Phil-CIA/Solar-Project-200w/hardware/mppt/net-plan.md

# MPPT Net Plan (Draft)

Last updated: 2026-07-14
Purpose: keep schematic net naming consistent and traceable from day one.

## 1. Naming Conventions

- Power nets: ALL_CAPS with domain and polarity suffix.
- Sense nets: SENSE_<DOMAIN>_<MEASURED>
- Control nets: CTRL_<FUNCTION>
- Fault nets: FAULT_<TYPE>
- Logging nets: UART_<DIR>_<ROLE>
- KiCad implementation style: use global labels for canonical inter-zone nets in the single-sheet schematic.
- Layout style: rectangles are used as functional zones (Sheet 1/2/3/4 intent), not separate hierarchical sheets.

## 2. Candidate Net List

| Net Name | Domain | Direction | Purpose | Requirement Link |
|---|---|---|---|---|
| PV_IN_POS_RAW | PV Input | In | Raw positive input before fuse and reverse protection | REQ-SAF-004 |
| PV_IN_POS_FUSED | PV Input | Internal | Positive input after fuse and before reverse protection element | REQ-SAF-004 |
| PV_IN_POS | PV Input | In | Positive PV input rail | REQ-PV-001 |
| PWR_NEG | Shared Return | Bidirectional | Canonical shared negative return rail across PV, charger output, and battery interface | REQ-PV-001, REQ-CHG-001, REQ-BAT-001 |
| MPPT_SW_NODE | Power Stage | Internal | Main switching node for conversion stage | REQ-CHG-001 |
| CHG_OUT_POS | Charger Output | Out | Charger positive output to battery interface | REQ-CHG-001 |
| BAT_BUS_POS | Battery Bus | Bidirectional | Battery positive bus boundary | REQ-BAT-001 |
| CTRL_SUPPLY_IN | Control Power | In | Protected control-domain input boundary after source OR-ing (PV and optional battery assist path) | REQ-SAF-003, REQ-TEL-002 |
| USB_5V_IN | Control Power | In | USB bench-power boundary used when PV is absent | REQ-TEL-001 |
| CTRL_3V3 | Control Power | Out | Main 3.3V control rail for STM32G431 digital supply and control I/O pull domains | REQ-TEL-002 |
| CTRL_3V3A | Control Power | Out | Filtered analog 3.3V rail for ADC/reference-sensitive nodes (can be linked to CTRL_3V3 in first pass) | REQ-TEL-002 |
| SENSE_PV_V | Sensing | In | PV voltage feedback channel | REQ-TEL-002 |
| SENSE_PV_I | Sensing | In | PV current feedback channel | REQ-TEL-002 |
| SENSE_BAT_V | Sensing | In | Battery voltage feedback channel | REQ-TEL-002 |
| SENSE_BAT_I | Sensing | In | Battery current feedback channel | REQ-TEL-002 |
| SENSE_TEMP_PWR | Sensing | In | Power stage thermal monitor | REQ-TEL-002 |
| SENSE_TEMP_BOARD | Sensing | In | Board ambient/control thermal monitor | REQ-TEL-002 |
| CTRL_PWM_MAIN | Control | Out | Main PWM drive/control command | REQ-CHG-001 |
| GATE_Q1 | Control | Out | Gate drive net to buck high-side MOSFET | REQ-CHG-001 |
| CTRL_EN_CHG | Control | Out | Charger enable/disable control | REQ-SAF-003 |
| BTN_UP_N | Control (UI) | In | Navigation button input (up), active-low | REQ-TEL-003 |
| BTN_DN_N | Control (UI) | In | Navigation button input (down), active-low | REQ-TEL-003 |
| BTN_LT_N | Control (UI) | In | Navigation button input (left), active-low | REQ-TEL-003 |
| BTN_RT_N | Control (UI) | In | Navigation button input (right), active-low | REQ-TEL-003 |
| BTN_ENT_N | Control (UI) | In | Navigation button input (enter/center), active-low | REQ-TEL-003 |
| FAULT_OCP | Protection | Out | Over-current fault signal | REQ-SAF-003 |
| FAULT_OVP | Protection | Out | Over-voltage fault signal | REQ-SAF-003 |
| UART_TX_LOG | Telemetry | Out | Serial logging transmitter | REQ-TEL-001 |
| UART_RX_CFG | Telemetry | In | Serial configuration/command receiver | REQ-TEL-001 |
| MCU_RST_N | Control | In | STM32 external reset net from button/debug path, active-low | REQ-SAF-006 |
| MCU_HSE_IN | Clock | In | STM32 external high-speed crystal input | REQ-VAL-003 |
| MCU_HSE_OUT | Clock | Out | STM32 external high-speed crystal output | REQ-VAL-003 |

## 3. Notes

- Final net names may evolve, but ID continuity should be preserved where possible.
- If a net name changes, update this file and record the reason in decisions-log.
- Current canonical negative return net is `PWR_NEG`; legacy per-zone negative names are retired for this single-sheet implementation.
- DEC-013 defines source-priority behavior for Rev 0 control power: PV-first runtime path, optional battery assist to `CTRL_SUPPLY_IN`, and protected USB fallback for bench operation when PV is absent.
- Q-004 is closed: the U4 wide-input control-supply path is the Rev 0 `CTRL_3V3` owner architecture; U2 path is not the intended live owner in final Rev 0 implementation.
