Phil-CIA/Solar-Project-200w/hardware/kicad/solar-project/report.txt

Info: Processing symbol 'C1:PCM_JLCPCB:C_0805'.
Info: Processing symbol 'C28:PCM_JLCPCB:C_0805'.
Info: Processing symbol 'C11:PCM_JLCPCB:C_1206'.
Info: Processing symbol 'R5:PCM_JLCPCB:R_0805'.
Info: Processing symbol 'C36:Capacitor_THT:CP_Radial_D6.3mm_P2.50mm'.
Info: Processing symbol 'R4:PCM_JLCPCB:R_0805'.
Info: Processing symbol 'R3:PCM_JLCPCB:R_0805'.
Info: Processing symbol 'R12:PCM_JLCPCB:R_0805'.
Info: Processing symbol 'L3:Inductor_SMD:L_KOHERelec_MDA7030'.
Info: Processing symbol 'C50:PCM_JLCPCB:C_0805'.
Info: Processing symbol 'D5:PCM_JLCPCB:D_DO-214AC(SMA)'.
Info: Processing symbol 'F1:Fuse:Fuseholder_Littelfuse_100_series_5x25mm'.
Info: Processing symbol 'C21:Capacitor_SMD:CP_Elec_10x12.6'.
Info: Processing symbol 'C2:PCM_JLCPCB:C_0805'.
Info: Processing symbol 'C12:PCM_JLCPCB:C_0805'.
Info: Processing symbol 'R6:PCM_JLCPCB:R_0805'.
Info: Processing symbol 'C29:PCM_JLCPCB:C_0805'.
Info: Processing symbol 'C44:PCM_JLCPCB:C_0805'.
Info: Processing symbol 'R2:PCM_JLCPCB:R_0805'.
Info: Processing symbol 'C37:Capacitor_THT:CP_Radial_D6.3mm_P2.50mm'.
Info: Processing symbol 'R14:PCM_JLCPCB:R_0805'.
Info: Processing symbol 'R26:PCM_JLCPCB:R_0805'.
Info: Processing symbol 'R25:PCM_JLCPCB:R_0805'.
Info: Processing symbol 'R23:PCM_JLCPCB:R_0805'.
Info: Processing symbol 'C3:Capacitor_THT:CP_Radial_D6.3mm_P2.50mm'.
Info: Processing symbol 'R22:Resistor_SMD:R_2512_6332Metric'.
Info: Processing symbol 'C13:PCM_JLCPCB:C_0805'.
Info: Processing symbol 'C22:PCM_JLCPCB:C_0805'.
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
Info: Processing symbol 'C27:PCM_JLCPCB:C_0805'.
Info: Processing symbol 'D9:PCM_JLCPCB:D_0805'.
Info: Processing symbol 'C35:PCM_JLCPCB:C_1206'.
Info: Processing symbol 'C10:PCM_JLCPCB:C_0805'.
Info: Processing symbol 'D4:PCM_JLCPCB:D_SOD-323'.
Info: Processing symbol 'C49:PCM_JLCPCB:C_0805'.
Info: Processing symbol 'R30:PCM_JLCPCB:R_0805'.
Info: Processing symbol 'R29:PCM_JLCPCB:R_0805'.
Info: Processing symbol 'R28:PCM_JLCPCB:R_0603'.
Info: Processing symbol 'J4:Connector_PinHeader_2.54mm:PinHeader_1x04_P2.54mm_Vertical_SMD_Pin1Right'.
Info: Processing symbol 'R27:PCM_JLCPCB:R_0805'.
Info: Processing symbol 'C20:PCM_JLCPCB:C_0805'.
Info: Processing symbol 'C43:Capacitor_THT:CP_Radial_D6.3mm_P2.50mm'.
Info: Processing symbol 'M3:Package_TO_SOT_SMD:TDSON-8-1'.
Info: Processing symbol 'R45:PCM_JLCPCB:R_0805'.
Info: Processing symbol 'R46:PCM_JLCPCB:R_0805'.
Info: Processing symbol 'R47:PCM_JLCPCB:R_0805'.
Info: Processing symbol 'R48:PCM_JLCPCB:R_0805'.
Info: Processing symbol 'R49:PCM_JLCPCB:R_0805'.
Info: Processing symbol 'R50:PCM_JLCPCB:R_0805'.
Info: Processing symbol 'R51:PCM_JLCPCB:R_0805'.
Info: Processing symbol 'R52:PCM_JLCPCB:R_0805'.
Info: Processing symbol 'R53:PCM_JLCPCB:R_0805'.
Info: Processing symbol 'R54:PCM_JLCPCB:R_0805'.
Info: Processing symbol 'R55:PCM_JLCPCB:R_0805'.
Info: Processing symbol 'R56:PCM_JLCPCB:R_0805'.
Info: Processing symbol 'R57:PCM_JLCPCB:R_0805'.
Info: Processing symbol 'R58:PCM_JLCPCB:R_0805'.
Info: Processing symbol 'R59:PCM_JLCPCB:R_0805'.
Info: Processing symbol 'R60:PCM_JLCPCB:R_0805'.
Info: Processing symbol 'R61:PCM_JLCPCB:R_0805'.
Info: Total warnings: 43, errors: 27.
Info: Processing symbol 'S1:PCM_JLCPCB:SW_TS-1088-AR02016'.
Info: Processing symbol 'SW1:PCM_JLCPCB:SW-SMD_4P-L5.1-W5.1-P3.70-LS6.5-TL-2'.
Info: Processing symbol 'SW2:PCM_JLCPCB:SW-SMD_4P-L5.1-W5.1-P3.70-LS6.5-TL-2'.
Info: Processing symbol 'SW3:PCM_JLCPCB:SW-SMD_4P-L5.1-W5.1-P3.70-LS6.5-TL-2'.
Info: Processing symbol 'SW4:PCM_JLCPCB:SW-SMD_4P-L5.1-W5.1-P3.70-LS6.5-TL-2'.
Info: Processing symbol 'SW5:PCM_JLCPCB:SW-SMD_4P-L5.1-W5.1-P3.70-LS6.5-TL-2'.
Info: Processing symbol 'TH1:'.
Info: Processing symbol 'TP1:Connector_PinHeader_2.54mm:PinHeader_1x01_P2.54mm_Vertical'.
Info: Processing symbol 'TP2:Connector_PinHeader_2.54mm:PinHeader_1x01_P2.54mm_Vertical'.
Info: Processing symbol 'TP3:Connector_PinHeader_2.54mm:PinHeader_1x01_P2.54mm_Vertical'.
Info: Processing symbol 'TP4:Connector_PinHeader_2.54mm:PinHeader_1x01_P2.54mm_Vertical'.
Info: Processing symbol 'TP5:Connector_PinHeader_2.54mm:PinHeader_1x01_P2.54mm_Vertical'.
Info: Processing symbol 'U1:Package_DFN_QFN:QFN-48-1EP_6x6mm_P0.4mm_EP4.4x4.4mm_ThermalVias'.
Info: Processing symbol 'U2:Package_SON:Infineon_PG-TDSON-8_6.15x5.15mm'.
Info: Processing symbol 'U3:PCM_JLCPCB:WQFN-28_L5.0-W5.0-P0.50-BL-EP3.2'.
Info: Processing symbol 'U4:PCM_JLCPCB:ESOP-8_L4.9-W3.9-P1.27-LS6.0-BL-EP'.
Info: Processing symbol 'U5:Package_SON:Infineon_PG-TDSON-8_6.15x5.15mm'.
Info: Processing symbol 'U6:Package_DFN_QFN:Texas_RHA0040B_VQFN-40-1EP_6x6mm_P0.5mm_EP4.15x4.15mm'.
Info: Processing symbol 'U7:1My_Parts_ ICs:Humidity sensor'.
Info: Processing symbol 'U8:1My_Parts_ ICs:0.96 inOLED display SSD1306'.
Info: Processing symbol 'U9:Package_SO:SOIC-8-1EP_3.9x4.9mm_P1.27mm_EP2.29x3mm_ThermalVias'.
Info: Processing symbol 'U10:PCM_JLCPCB:SOT-363_SC-70-6'.
Info: Processing symbol 'X2:PCM_JLCPCB:CRYSTAL-SMD_L11.5-W4.8-LS12.7'.
Connected C4 pin 1 to PWR_NEG.
Connected C4 pin 2 to V_out.
Added C5 (footprint 'Capacitor_THT:CP_Radial_D6.3mm_P2.50mm').
Changed REF** reference designator to C5.
Changed C5 value from CP_Radial_D6.3mm_P2.50mm to 47uf.
Updated C5 symbol association from  to /53480408-6937-45d7-bc8f-def0286907a6.
Updated C5 fields.
Updated C5 sheetname to '/'.
Updated C5 sheetfile to 'Solar Project.kicad_sch'.
Updated C5 footprint filters to 'C_*'.
Connected C5 pin 1 to V_out.
Connected C5 pin 2 to PWR_NEG.
Added C6 (footprint 'Capacitor_THT:CP_Radial_D6.3mm_P2.50mm').
Changed REF** reference designator to C6.
Changed C6 value from CP_Radial_D6.3mm_P2.50mm to 47uf.
Updated C6 symbol association from  to /48637952-fe6a-4e5a-8483-2ea2f98bf761.
Updated C6 fields.
Updated C6 sheetname to '/'.
Updated C6 sheetfile to 'Solar Project.kicad_sch'.
Updated C6 footprint filters to 'C_*'.
Connected C6 pin 1 to PWR_NEG.
Connected C6 pin 2 to V_out.
Added C7 (footprint 'PCM_JLCPCB:C_1206').
Changed REF** reference designator to C7.
Changed C7 value from C_1206_3216Metric to 2.2uF.
Updated C7 symbol association from  to /7768fee7-d3f5-4536-9321-ae11860275cd.
Updated C7 fields.
Updated C7 sheetname to '/'.
Updated C7 sheetfile to 'Solar Project.kicad_sch'.
Updated C7 footprint filters to 'C_*'.
Connected C7 pin 2 to PWR_NEG.
Add net PV_IN_POS.
Connected C7 pin 1 to PV_IN_POS.
Added C8 (footprint 'PCM_JLCPCB:C_1206').
Changed REF** reference designator to C8.
Changed C8 value from C_1206_3216Metric to 2.2uF.
Updated C8 symbol association from  to /75bb1e57-b422-47de-b2ef-34c1778d920a.
Updated C8 fields.
Updated C8 sheetname to '/'.
Updated C8 sheetfile to 'Solar Project.kicad_sch'.
Updated C8 footprint filters to 'C_*'.
Connected C8 pin 1 to PWR_NEG.
Connected C8 pin 2 to PV_IN_POS.
Added C9 (footprint 'PCM_JLCPCB:C_0805').
Changed REF** reference designator to C9.
Changed C9 value from C_0805_2012Metric to 2.2nF.
Updated C9 symbol association from  to /298997c7-a62c-4105-a012-c2c29bfdbec9.
Updated C9 fields.
Updated C9 sheetname to '/'.
Updated C9 sheetfile to 'Solar Project.kicad_sch'.
Updated C9 footprint filters to 'C_*'.
Add net Net-(C10-Pad1).
Connected C9 pin 2 to Net-(C10-Pad1).
Add net CTRL_3V3.
Connected C9 pin 1 to CTRL_3V3.
Added C10 (footprint 'PCM_JLCPCB:C_0805').
Changed REF** reference designator to C10.
Changed C10 value from C_0805_2012Metric to 47pF.
Updated C10 symbol association from  to /0278144f-d8a0-44aa-b98a-90d45dd2aeed.
Updated C10 fields.
Updated C10 sheetname to '/'.
Updated C10 sheetfile to 'Solar Project.kicad_sch'.
Updated C10 footprint filters to 'C_*'.
Add net Net-(U4-FB).
Connected C10 pin 2 to Net-(U4-FB).
Connected C10 pin 1 to Net-(C10-Pad1).
Added C11 (footprint 'PCM_JLCPCB:C_1206').
Changed REF** reference designator to C11.
Changed C11 value from C_1206_3216Metric to 2.2uF.
Updated C11 symbol association from  to /51d65eb5-b2e8-45e4-b06b-f7ecfab86fc1.
Updated C11 fields.
Updated C11 sheetname to '/'.
Updated C11 sheetfile to 'Solar Project.kicad_sch'.
Updated C11 footprint filters to 'C_*'.
Connected C11 pin 1 to PWR_NEG.
Connected C11 pin 2 to PV_IN_POS.
Added C12 (footprint 'PCM_JLCPCB:C_0805').
Changed REF** reference designator to C12.
Changed C12 value from C_0805_2012Metric to 100nF.
Updated C12 symbol association from  to /96c903d8-4aa3-41cf-a6ba-836a83798078.
Updated C12 fields.
Updated C12 sheetname to '/'.
Updated C12 sheetfile to 'Solar Project.kicad_sch'.
Updated C12 footprint filters to 'C_*'.
Connected C12 pin 1 to CTRL_3V3.
Connected C12 pin 2 to PWR_NEG.
Added C13 (footprint 'PCM_JLCPCB:C_0805').
Changed REF** reference designator to C13.
Changed C13 value from C_0805_2012Metric to 2.2nF.
Updated C13 symbol association from  to /5476fed9-09df-498b-b3bf-14cd4dcbb424.
Updated C13 fields.
Updated C13 sheetname to '/'.
Updated C13 sheetfile to 'Solar Project.kicad_sch'.
Updated C13 footprint filters to 'C_*'.
Add net Net-(U4-SW).
Connected C13 pin 1 to Net-(U4-SW).
Add net Net-(U4-BST).
Connected C13 pin 2 to Net-(U4-BST).
Added C14 (footprint 'PCM_JLCPCB:C_1206').
Changed REF** reference designator to C14.
Changed C14 value from C_1206_3216Metric to 100uF.
Updated C14 symbol association from  to /4221db3a-9608-4efe-aa9f-f7902025f264.
Updated C14 fields.
Updated C14 sheetname to '/'.
Updated C14 sheetfile to 'Solar Project.kicad_sch'.
Updated C14 footprint filters to 'C_*'.
Connected C14 pin 1 to CTRL_3V3.
Connected C14 pin 2 to PWR_NEG.
Added C15 (footprint 'PCM_JLCPCB:C_1206').
Changed REF** reference designator to C15.
Changed C15 value from C_1206_3216Metric to 2.2uF.
Updated C15 symbol association from  to /1e7e7a8a-90f1-4720-b42c-6e6d8a8ae7c1.
Updated C15 fields.
Updated C15 sheetname to '/'.
Updated C15 sheetfile to 'Solar Project.kicad_sch'.
Updated C15 footprint filters to 'C_*'.
Connected C15 pin 2 to PWR_NEG.
Add net Net-(U4-VIN).
Connected C15 pin 1 to Net-(U4-VIN).
Added C16 (footprint 'Capacitor_SMD:CP_Elec_6.3x7.7').
Changed REF** reference designator to C16.
Changed C16 value from CP_Elec_6.3x7.7 to 10uf.
Updated C16 symbol association from  to /a78c6225-23fe-4c44-9335-dc416b9e6acf.
Updated C16 fields.
Updated C16 sheetname to '/'.
Updated C16 sheetfile to 'Solar Project.kicad_sch'.
Updated C16 footprint filters to 'C_*'.
Connected C16 pin 2 to PWR_NEG.
Connected C16 pin 1 to PV_IN_POS.
Added C17 (footprint 'Capacitor_THT:CP_Radial_D6.3mm_P2.50mm').
Changed REF** reference designator to C17.
Changed C17 value from CP_Radial_D6.3mm_P2.50mm to 47uf.
Updated C17 symbol association from  to /4ff70a42-d926-4abd-b6ab-268b79878f0f.
Updated C17 fields.
Updated C17 sheetname to '/'.
Updated C17 sheetfile to 'Solar Project.kicad_sch'.
Updated C17 footprint filters to 'C_*'.
Connected C17 pin 1 to V_out.
Connected C17 pin 2 to PWR_NEG.
Added C18 (footprint 'Capacitor_SMD:CP_Elec_10x12.6').
Changed REF** reference designator to C18.
Changed C18 value from CP_Elec_10x12.6 to 560uf.
Updated C18 symbol association from  to /784c021b-9ccb-4a28-9b9b-923df4e90088.
Updated C18 fields.
Updated C18 sheetname to '/'.
Updated C18 sheetfile to 'Solar Project.kicad_sch'.
Updated C18 footprint filters to 'C_*'.
Connected C18 pin 1 to V_out.
Connected C18 pin 2 to PWR_NEG.
Added C19 (footprint 'Capacitor_THT:CP_Radial_D6.3mm_P2.50mm').
Changed REF** reference designator to C19.
Changed C19 value from CP_Radial_D6.3mm_P2.50mm to 47uf.
Updated C19 symbol association from  to /46402b25-b4b4-4a80-b24c-0a1f6d254ed2.
Updated C19 fields.
Updated C19 sheetname to '/'.
Updated C19 sheetfile to 'Solar Project.kicad_sch'.
Updated C19 footprint filters to 'C_*'.
Connected C19 pin 1 to PV_IN_POS.
Connected C19 pin 2 to PWR_NEG.
Added C20 (footprint 'PCM_JLCPCB:C_0805').
Changed REF** reference designator to C20.
Changed C20 value from C_0805_2012Metric to 180pf.
Updated C20 symbol association from  to /9054d6ca-fc1c-49c5-a332-e5169c3210f8.
Updated C20 fields.
Updated C20 sheetname to '/'.
Updated C20 sheetfile to 'Solar Project.kicad_sch'.
Updated C20 footprint filters to 'C_*'.
Add net Net-(U6-CSA).
Connected C20 pin 1 to Net-(U6-CSA).
Add net Net-(U6-CSB).
Connected C20 pin 2 to Net-(U6-CSB).
Added C21 (footprint 'Capacitor_SMD:CP_Elec_10x12.6').
Changed REF** reference designator to C21.
Changed C21 value from CP_Elec_10x12.6 to 560uf.
Updated C21 symbol association from  to /6af53501-8f64-4a2e-a6ce-146c598d6e8b.
Updated C21 fields.
Updated C21 sheetname to '/'.
Updated C21 sheetfile to 'Solar Project.kicad_sch'.
Updated C21 footprint filters to 'C_*'.
Connected C21 pin 1 to V_out.
Connected C21 pin 2 to PWR_NEG.
Added C22 (footprint 'PCM_JLCPCB:C_0805').
Changed REF** reference designator to C22.
Changed C22 value from C_0805_2012Metric to 100nF.
Updated C22 symbol association from  to /49c76ce8-b475-4eb9-9590-b65484c0b54b.
Updated C22 fields.
Updated C22 sheetname to '/'.
Updated C22 sheetfile to 'Solar Project.kicad_sch'.
Updated C22 footprint filters to 'C_*'.
Add net Net-(U6-HB1).
Connected C22 pin 1 to Net-(U6-HB1).
Add net SW_1.
Connected C22 pin 2 to SW_1.
Added C23 (footprint 'PCM_JLCPCB:C_0805').
Changed REF** reference designator to C23.
Changed C23 value from C_0805_2012Metric to 100nf.
Updated C23 symbol association from  to /5eb4a86f-4c87-4a9f-80ea-932d9fce766f.
Updated C23 fields.
Updated C23 sheetname to '/'.
Updated C23 sheetfile to 'Solar Project.kicad_sch'.
Add net SW_2.
Connected C23 pin 2 to SW_2.
Add net Net-(U6-HB2).
Connected C23 pin 1 to Net-(U6-HB2).
Added C24 (footprint 'PCM_JLCPCB:C_0805').
Changed REF** reference designator to C24.
Changed C24 value from C_0805_2012Metric to 220nf.
Updated C24 symbol association from  to /9e38ad1e-7ad7-44cc-80b0-d5384aa204a9.
Updated C24 fields.
Updated C24 sheetname to '/'.
Updated C24 sheetfile to 'Solar Project.kicad_sch'.
Updated C24 footprint filters to 'C_*'.
Add net Net-(U6-COMP).
Connected C24 pin 2 to Net-(U6-COMP).
Add net Net-(C24-Pad1).
Connected C24 pin 1 to Net-(C24-Pad1).
Added C25 (footprint 'PCM_JLCPCB:C_0805').
Changed REF** reference designator to C25.
Changed C25 value from C_0805_2012Metric to 1.5nf.
Updated C25 symbol association from  to /87c5de80-fb7a-41bc-a8dc-f608aa31b815.
Updated C25 fields.
Updated C25 sheetname to '/'.
Updated C25 sheetfile to 'Solar Project.kicad_sch'.
Updated C25 footprint filters to 'C_*'.
Connected C25 pin 2 to Net-(U6-COMP).
Add net PGND.
Connected C25 pin 1 to PGND.
Added C26 (footprint 'PCM_JLCPCB:C_0805').
Changed REF** reference designator to C26.
Changed C26 value from C_0805_2012Metric to 33nf.
Updated C26 symbol association from  to /7c85752c-5bd5-4bdf-8446-302b07c3f9f1.
Updated C26 fields.
Updated C26 sheetname to '/'.
Updated C26 sheetfile to 'Solar Project.kicad_sch'.
Updated C26 footprint filters to 'C_*'.
Connected C26 pin 1 to PGND.
Add net Net-(U6-SS_ATRK).
Connected C26 pin 2 to Net-(U6-SS_ATRK).
Added C27 (footprint 'PCM_JLCPCB:C_0805').
Changed REF** reference designator to C27.
Changed C27 value from C_0805_2012Metric to 22uF.
Updated C27 symbol association from  to /77976eb9-834e-4d64-bc9b-614dc9146d92.
Updated C27 fields.
Updated C27 sheetname to '/'.
Updated C27 sheetfile to 'Solar Project.kicad_sch'.
Updated C27 footprint filters to 'C_*'.
Connected C27 pin 2 to PGND.
Add net Net-(U6-VCC1).
Connected C27 pin 1 to Net-(U6-VCC1).
Added C28 (footprint 'PCM_JLCPCB:C_0805').
Changed REF** reference designator to C28.
Changed C28 value from C_0805_2012Metric to 100nF.
Updated C28 symbol association from  to /f203cc23-b51f-4c4d-924f-517e9417f31c.
Updated C28 fields.
Updated C28 sheetname to '/'.
Updated C28 sheetfile to 'Solar Project.kicad_sch'.
Updated C28 footprint filters to 'C_*'.
Connected C28 pin 1 to PV_IN_POS.
Connected C28 pin 2 to PWR_NEG.
Added C29 (footprint 'PCM_JLCPCB:C_0805').
Changed REF** reference designator to C29.
Changed C29 value from C_0805_2012Metric to 22uF.
Updated C29 symbol association from  to /64b79659-6b78-4dea-a259-213377790cfb.
Updated C29 fields.
Updated C29 sheetname to '/'.
Updated C29 sheetfile to 'Solar Project.kicad_sch'.
Updated C29 footprint filters to 'C_*'.
Add net U6_VCC2.
Connected C29 pin 1 to U6_VCC2.
Connected C29 pin 2 to PWR_NEG.
Added C30 (footprint 'Capacitor_THT:CP_Radial_D6.3mm_P2.50mm').
Changed REF** reference designator to C30.
Changed C30 value from CP_Radial_D6.3mm_P2.50mm to 47uf.
Updated C30 symbol association from  to /6d669fdc-962e-4b20-8f30-7ee6e9c55ec5.
Updated C30 fields.
Updated C30 sheetname to '/'.
Updated C30 sheetfile to 'Solar Project.kicad_sch'.
Updated C30 footprint filters to 'C_*'.
Connected C30 pin 2 to V_out.
Connected C30 pin 1 to PWR_NEG.
Added C31 (footprint 'Capacitor_THT:CP_Radial_D6.3mm_P2.50mm').
Changed REF** reference designator to C31.
Changed C31 value from CP_Radial_D6.3mm_P2.50mm to 47uf.
Updated C31 symbol association from  to /06f9af03-fc83-4d46-93e9-32d4107cb657.
Updated C31 fields.
Updated C31 sheetname to '/'.
Updated C31 sheetfile to 'Solar Project.kicad_sch'.
Updated C31 footprint filters to 'C_*'.
Connected C31 pin 2 to V_out.
Connected C31 pin 1 to PWR_NEG.
Added C32 (footprint 'Capacitor_THT:CP_Radial_D6.3mm_P2.50mm').
Changed REF** reference designator to C32.
Changed C32 value from CP_Radial_D6.3mm_P2.50mm to 47uf.
Updated C32 symbol association from  to /912557a7-39f8-4810-bf9e-c982684d216a.
Updated C32 fields.
Updated C32 sheetname to '/'.
Updated C32 sheetfile to 'Solar Project.kicad_sch'.
Updated C32 footprint filters to 'C_*'.
Connected C32 pin 2 to PWR_NEG.
Connected C32 pin 1 to PV_IN_POS.
Added C33 (footprint 'PCM_JLCPCB:C_1206').
Changed REF** reference designator to C33.
Changed C33 value from C_1206_3216Metric to 2.2uF.
Updated C33 symbol association from  to /5cf9fa44-b585-4ada-b72a-ebd62a77c70c.
Updated C33 fields.
Updated C33 sheetname to '/'.
Updated C33 sheetfile to 'Solar Project.kicad_sch'.
Updated C33 footprint filters to 'C_*'.
Connected C33 pin 1 to V_out.
Connected C33 pin 2 to PWR_NEG.
Added C34 (footprint 'PCM_JLCPCB:C_1206').
Changed REF** reference designator to C34.
Changed C34 value from C_1206_3216Metric to 2.2uF.
Updated C34 symbol association from  to /4cbf5b2a-d68a-431e-9cb9-b4a607a96a75.
Updated C34 fields.
Updated C34 sheetname to '/'.
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
Connected C43 pin 1 to PWR_NEG.
Added C44 (footprint 'PCM_JLCPCB:C_0805').
Changed REF** reference designator to C44.
Changed C44 value from C_0805_2012Metric to 100nF.
Updated C44 symbol association from  to /9583469a-2efe-4c14-a4d7-d1c925e87bf7.
Updated C44 fields.
Updated C44 sheetname to '/'.
Updated C44 sheetfile to 'Solar Project.kicad_sch'.
Updated C44 footprint filters to 'C_*'.
Connected C44 pin 2 to PWR_NEG.
Connected C44 pin 1 to CTRL_3V3.
Added C45 (footprint 'PCM_JLCPCB:C_0805').
Changed REF** reference designator to C45.
Changed C45 value from C_0805_2012Metric to 100nF.
Updated C45 symbol association from  to /5149388b-e43d-4cd7-a492-814eec618702.
Updated C45 fields.
Updated C45 sheetname to '/'.
Updated C45 sheetfile to 'Solar Project.kicad_sch'.
Updated C45 footprint filters to 'C_*'.
Connected C45 pin 2 to PWR_NEG.
Connected C45 pin 1 to U6_VCC2.
Added C46 (footprint 'PCM_JLCPCB:C_0805').
Changed REF** reference designator to C46.
Changed C46 value from C_0805_2012Metric to 100nF.
Updated C46 symbol association from  to /24f1ea32-9f91-4ed1-b226-00067150747f.
Updated C46 fields.
Updated C46 sheetname to '/'.
Updated C46 sheetfile to 'Solar Project.kicad_sch'.
Updated C46 footprint filters to 'C_*'.
Connected C46 pin 1 to Net-(U6-VCC1).
Connected C46 pin 2 to PGND.
Updated C23 footprint filters to 'C_*'.
Added C47 (footprint 'PCM_JLCPCB:C_0805').
Changed REF** reference designator to C47.
Changed C47 value from C_0805_2012Metric to 100nF.
Updated C47 symbol association from  to /948366cf-8d0a-4b69-978c-3a15cd0e398f.
Updated C47 fields.
Updated C47 sheetname to '/'.
Updated C47 sheetfile to 'Solar Project.kicad_sch'.
Updated C47 footprint filters to 'C_*'.
Connected C47 pin 2 to PWR_NEG.
Add net Net-(S1-A).
Connected C47 pin 1 to Net-(S1-A).
Added C48 (footprint 'PCM_JLCPCB:C_0805').
Changed REF** reference designator to C48.
Changed C48 value from C_0805_2012Metric to 100nF.
Updated C48 symbol association from  to /864e01de-909c-4b18-ba52-a4d9d23b3b76.
Updated C48 fields.
Updated C48 sheetname to '/'.
Updated C48 sheetfile to 'Solar Project.kicad_sch'.
Updated C48 footprint filters to 'C_*'.
Connected C48 pin 1 to CTRL_3V3.
Connected C48 pin 2 to PWR_NEG.
Added C49 (footprint 'PCM_JLCPCB:C_0805').
Changed REF** reference designator to C49.
Changed C49 value from C_0805_2012Metric to 33pF.
Updated C49 symbol association from  to /c57b5c97-32c1-40da-aa9d-ce518ffe7aa9.
Updated C49 fields.
Updated C49 sheetname to '/'.
Updated C49 sheetfile to 'Solar Project.kicad_sch'.
Updated C49 footprint filters to 'C_*'.
Add net Net-(U1-PF1-OSC_OUT).
Connected C49 pin 1 to Net-(U1-PF1-OSC_OUT).
Connected C49 pin 2 to PWR_NEG.
Added C50 (footprint 'PCM_JLCPCB:C_0805').
Changed REF** reference designator to C50.
Changed C50 value from C_0805_2012Metric to 33pF.
Updated C50 symbol association from  to /9f3a2ad3-9403-42e9-a1f0-2450c841f458.
Updated C50 fields.
Updated C50 sheetname to '/'.
Updated C50 sheetfile to 'Solar Project.kicad_sch'.
Updated C50 footprint filters to 'C_*'.
Connected C50 pin 2 to PWR_NEG.
Add net Net-(U1-PF0-OSC_IN).
Connected C50 pin 1 to Net-(U1-PF0-OSC_IN).
Added D1 (footprint 'PCM_JLCPCB:D_DO-214AC(SMA)').
Changed REF** reference designator to D1.
Changed D1 value from SMA_L4.5-W2.6-LS5.1-RD to 1SMA4742A.
Updated D1 symbol association from  to /cc7dd454-6dbc-40b3-8a3a-e6a649ae578b.
Updated D1 fields.
Updated D1 sheetname to '/'.
Updated D1 sheetfile to 'Solar Project.kicad_sch'.
Updated D1 footprint filters to 'D_*'.
Add net Net-(U2-S1).
Connected D1 pin 2 to Net-(U2-S1).
Add net Net-(U2-G1).
Connected D1 pin 1 to Net-(U2-G1).
Added D2 (footprint 'PCM_JLCPCB:D_SMB').
Changed REF** reference designator to D2.
Changed D2 value from D_SMB to SMBJ60CA.
Updated D2 symbol association from  to /d91785c2-8ab3-4127-a0f0-b02862cca018.
Updated D2 fields.
Updated D2 sheetname to '/'.
Updated D2 sheetfile to 'Solar Project.kicad_sch'.
Updated D2 footprint filters to 'D_*'.
Add net /PV_IN_POS_FUSED.
Connected D2 pin 2 to /PV_IN_POS_FUSED.
Connected D2 pin 1 to PWR_NEG.
Added D3 (footprint 'digikey-footprints:SOT23-6L').
Changed REF** reference designator to D3.
Changed D3 value from SOT23-6L to USBLC6-2SC6.
Updated D3 symbol association from  to /543c3cc0-b720-47d8-981d-5fe01dd798eb.
Updated D3 fields.
Updated D3 sheetname to '/'.
Updated D3 sheetfile to 'Solar Project.kicad_sch'.
Add net Net-(U3-D+).
Connected D3 pin 4 to Net-(U3-D+).
Add net Net-(U3-D-).
Connected D3 pin 6 to Net-(U3-D-).
Add net Net-(D3-Pad1).
Connected D3 pin 1 to Net-(D3-Pad1).
Connected D3 pin 2 to PWR_NEG.
Add net Net-(D3-Pad3).
Connected D3 pin 3 to Net-(D3-Pad3).
Connected D3 pin 5 to VBUS.
Added D4 (footprint 'PCM_JLCPCB:D_SOD-323').
Changed REF** reference designator to D4.
Changed D4 value from D_SOD-323 to 1N5819WS.
Updated D4 symbol association from  to /92caf6c3-412e-4b95-8303-2eadf3bfacb9.
Updated D4 fields.
Updated D4 sheetname to '/'.
Updated D4 sheetfile to 'Solar Project.kicad_sch'.
Updated D4 footprint filters to 'D_*'.
Connected D4 pin 1 to Net-(U4-VIN).
Add net BAT_BUS_POS.
Connected D4 pin 2 to BAT_BUS_POS.
Added D5 (footprint 'PCM_JLCPCB:D_DO-214AC(SMA)').
Changed REF** reference designator to D5.
Changed D5 value from SMA_L4.5-W2.6-LS5.1-RD to 1SMA4742A.
Updated D5 symbol association from  to /1004903f-0aa1-4004-82a4-f4e21d23257d.
Updated D5 fields.
Updated D5 sheetname to '/'.
Updated D5 sheetfile to 'Solar Project.kicad_sch'.
Updated D5 footprint filters to 'D_*'.
Add net Net-(U5-G1).
Connected D5 pin 1 to Net-(U5-G1).
Add net Net-(U5-S1).
Connected D5 pin 2 to Net-(U5-S1).
Added D6 (footprint 'PCM_JLCPCB:D_SOD-323').
Changed REF** reference designator to D6.
Changed D6 value from D_SOD-323 to 1N5819WS.
Updated D6 symbol association from  to /d6a1b2c3-d4e5-6789-abcd-ef0123456789.
Updated D6 fields.
Updated D6 sheetname to '/'.
Updated D6 sheetfile to 'Solar Project.kicad_sch'.
Updated D6 footprint filters to 'D_*'.
Connected D6 pin 1 to Net-(U4-VIN).
Add net CHG_OUT_POS.
Connected D6 pin 2 to CHG_OUT_POS.
Added D7 (footprint 'PCM_JLCPCB:D_SOD-323').
Changed REF** reference designator to D7.
Changed D7 value from D_SOD-323 to 1N5819WS.
Updated D7 symbol association from  to /d7a1b2c3-d4e5-6789-abcd-ef0123456789.
Updated D7 fields.
Updated D7 sheetname to '/'.
Updated D7 sheetfile to 'Solar Project.kicad_sch'.
Updated D7 footprint filters to 'D_*'.
Connected D7 pin 1 to Net-(U4-VIN).
Connected D7 pin 2 to VBUS.
Added D8 (footprint 'PCM_JLCPCB:LED-SMD_4P-L1.6-W1.5_XL-1615RGBC-WS2812B').
Changed REF** reference designator to D8.
Changed D8 value from LED-SMD_4P-L1.6-W1.5_XL-1615RGBC-WS2812B to WS2812B.
Updated D8 symbol association from  to /b8235dd6-007a-4515-b865-7404793a3822.
Updated D8 fields.
Updated D8 sheetname to '/'.
Updated D8 sheetfile to 'Solar Project.kicad_sch'.
Connected D8 pin 3 to PWR_NEG.
Add net unconnected-(D8-DOUT-Pad1).
Connected D8 pin 1 to unconnected-(D8-DOUT-Pad1).
Add net Net-(D8-DIN).
Connected D8 pin 4 to Net-(D8-DIN).
Connected D8 pin 2 to U6_VCC2.
Added D9 (footprint 'PCM_JLCPCB:D_0805').
Changed REF** reference designator to D9.
Changed D9 value from LED_0805_2012Metric to Yellow.
Updated D9 symbol association from  to /8668a948-4b0e-408a-8c94-37978fca1cdd.
Updated D9 fields.
Updated D9 sheetname to '/'.
Updated D9 sheetfile to 'Solar Project.kicad_sch'.
Updated D9 footprint filters to 'D_*'.
Connected D9 pin 1 to PWR_NEG.
Add net Net-(D9-Pad2).
Connected D9 pin 2 to Net-(D9-Pad2).
Added F1 (footprint 'Fuse:Fuseholder_Littelfuse_100_series_5x25mm').
Changed REF** reference designator to F1.
Changed F1 value from Fuseholder_Littelfuse_100_series_5x25mm to 10 amp.
Updated F1 symbol association from  to /198960ae-07e2-4352-bf45-3afdce5d8176.
Updated F1 fields.
Updated F1 sheetname to '/'.
Updated F1 sheetfile to 'Solar Project.kicad_sch'.
Updated F1 footprint filters to '*Fuse*'.
Add net /PV_IN_POS_RAW.
Connected F1 pin 2 to /PV_IN_POS_RAW.
Connected F1 pin 2 to /PV_IN_POS_RAW.
Connected F1 pin 1 to /PV_IN_POS_FUSED.
Connected F1 pin 1 to /PV_IN_POS_FUSED.
Added F2 (footprint 'Fuse:Fuseholder_Littelfuse_100_series_5x25mm').
Changed REF** reference designator to F2.
Changed F2 value from Fuseholder_Littelfuse_100_series_5x25mm to Fuse.
Updated F2 symbol association from  to /410e231d-992b-4575-ac5d-256dca83a38e.
Updated F2 fields.
Updated F2 sheetname to '/'.
Updated F2 sheetfile to 'Solar Project.kicad_sch'.
Updated F2 footprint filters to '*Fuse*'.
Connected F2 pin 2 to BAT_BUS_POS.
Connected F2 pin 1 to CHG_OUT_POS.
Connected F2 pin 2 to BAT_BUS_POS.
Connected F2 pin 1 to CHG_OUT_POS.
Added J1 (footprint 'TerminalBlock_Phoenix:TerminalBlock_Phoenix_MKDS-1,5-2-5.08_1x02_P5.08mm_Horizontal').
Changed REF** reference designator to J1.
Changed J1 value from TerminalBlock_Phoenix_MKDS-1,5-2-5.08_1x02_P5.08mm_Horizontal to Solar In.
Updated J1 symbol association from  to /7579c1f8-edbb-4420-8064-350147539ee2.
Updated J1 fields.
Updated J1 sheetname to '/'.
Updated J1 sheetfile to 'Solar Project.kicad_sch'.
Updated J1 footprint filters to 'TerminalBlock*:*'.
Connected J1 pin 2 to PWR_NEG.
Connected J1 pin 1 to /PV_IN_POS_RAW.
Added J3 (footprint 'TerminalBlock_Phoenix:TerminalBlock_Phoenix_MKDS-1,5-2-5.08_1x02_P5.08mm_Horizontal').
Changed REF** reference designator to J3.
Changed J3 value from TerminalBlock_Phoenix_MKDS-1,5-2-5.08_1x02_P5.08mm_Horizontal to Battery Bus.
Updated J3 symbol association from  to /afbea1e0-2291-4316-b74f-8835d6f936c5.
Updated J3 fields.
Updated J3 sheetname to '/'.
Updated J3 sheetfile to 'Solar Project.kicad_sch'.
Updated J3 footprint filters to 'TerminalBlock*:*'.
Connected J3 pin 1 to BAT_BUS_POS.
Connected J3 pin 2 to PWR_NEG.
Added J4 (footprint 'Connector_PinHeader_2.54mm:PinHeader_1x04_P2.54mm_Vertical_SMD_Pin1Right').
Changed REF** reference designator to J4.
Changed J4 value from PinHeader_1x04_P2.54mm_Vertical_SMD_Pin1Right to JTAG.
Updated J4 symbol association from  to /f5fd4157-0b37-4c0e-b1bf-8d8641df9502.
Updated J4 fields.
Updated J4 sheetname to '/'.
Updated J4 sheetfile to 'Solar Project.kicad_sch'.
Updated J4 footprint filters to 'Connector*:*_1x??_*'.
Add net SWCLK.
Connected J4 pin 1 to SWCLK.
Add net SWDIO.
Connected J4 pin 2 to SWDIO.
Connected J4 pin 4 to PWR_NEG.
Add net unconnected-(J4-Pin_3-Pad3).
Connected J4 pin 3 to unconnected-(J4-Pin_3-Pad3).
Added J5 (footprint 'Connector_USB:USB_C_Receptacle_G-Switch_GT-USB-7010ASV').
Changed REF** reference designator to J5.
Changed J5 value from USB_C_Receptacle_G-Switch_GT-USB-7010ASV to Connector,_USB-TYPE-C-16P.
Updated J5 symbol association from  to /eef5d84a-747e-48f2-b122-e9f791f00282.
Updated J5 fields.
Updated J5 sheetname to '/'.
Updated J5 sheetfile to 'Solar Project.kicad_sch'.
Connected J5 pin S1 to PWR_NEG.
Connected J5 pin S1 to PWR_NEG.
Add net Net-(J5-CC2).
Connected J5 pin B5 to Net-(J5-CC2).
Connected J5 pin A7 to Net-(D3-Pad1).
Add net Net-(J5-SBU1).
Connected J5 pin B8 to Net-(J5-SBU1).
Connected J5 pin A8 to Net-(J5-SBU1).
Connected J5 pin B7 to Net-(D3-Pad1).
Connected J5 pin S1 to PWR_NEG.
Connected J5 pin S1 to PWR_NEG.
Connected J5 pin B6 to Net-(D3-Pad3).
Add net Net-(J5-CC1).
Connected J5 pin A5 to Net-(J5-CC1).
Connected J5 pin A6 to Net-(D3-Pad3).
Added L2 (footprint '1My_Parts_ Passive:HC3-1R0-R').
Changed REF** reference designator to L2.
Changed L2 value from HC3-1R0-R to 1uh.
Updated L2 symbol association from  to /88a15297-ec04-455e-b13e-bb83c0c3634e.
Updated L2 fields.
Updated L2 sheetname to '/'.
Updated L2 sheetfile to 'Solar Project.kicad_sch'.
Updated L2 footprint filters to 'Choke_* *Coil* Inductor_* L_*'.
Add net Net-(L2-Pad1).
Connected L2 pin 1 to Net-(L2-Pad1).
Connected L2 pin 2 to SW_2.
Added L3 (footprint 'Inductor_SMD:L_KOHERelec_MDA7030').
Changed REF** reference designator to L3.
Changed L3 value from L_KOHERelec_MDA7030 to 68uh.
Updated L3 symbol association from  to /d67279e0-cd7a-4027-a847-53c484106090.
Updated L3 fields.
Updated L3 sheetname to '/'.
Updated L3 sheetfile to 'Solar Project.kicad_sch'.
Updated L3 footprint filters to 'Choke_* *Coil* Inductor_* L_*'.
Connected L3 pin 2 to CTRL_3V3.
Connected L3 pin 1 to Net-(U4-SW).
Added M1 (footprint 'Package_TO_SOT_SMD:TDSON-8-1').
Changed REF** reference designator to M1.
Changed M1 value from TDSON-8-1 to IPZ40N.
Updated M1 symbol association from  to /b3378798-6fc9-4b50-857e-6289b3dd260f.
Updated M1 fields.
Updated M1 sheetname to '/'.
Updated M1 sheetfile to 'Solar Project.kicad_sch'.
Added M2 (footprint 'Package_TO_SOT_SMD:TDSON-8-1').
Changed REF** reference designator to M2.
Changed M2 value from TDSON-8-1 to IPZ40N.
Updated M2 symbol association from  to /35a4e79a-9eff-4212-a8c1-5a008b2bd317.
Updated M2 fields.
Updated M2 sheetname to '/'.
Updated M2 sheetfile to 'Solar Project.kicad_sch'.
Added M3 (footprint 'Package_TO_SOT_SMD:TDSON-8-1').
Changed REF** reference designator to M3.
Changed M3 value from TDSON-8-1 to IPZ40N.
Updated M3 symbol association from  to /2174e2a6-5166-4544-9154-c4839ce52202.
Updated M3 fields.
Updated M3 sheetname to '/'.
Updated M3 sheetfile to 'Solar Project.kicad_sch'.
Added M4 (footprint 'Package_TO_SOT_SMD:TDSON-8-1').
Changed REF** reference designator to M4.
Changed M4 value from TDSON-8-1 to IPZ40N.
Updated M4 symbol association from  to /76693bae-fd8f-4042-9a1d-1885e33c0eed.
Updated M4 fields.
Updated M4 sheetname to '/'.
Updated M4 sheetfile to 'Solar Project.kicad_sch'.
Added Q1 (footprint 'PCM_JLCPCB:Q_SOT-23').
Changed REF** reference designator to Q1.
Changed Q1 value from SOT-23 to BSS138.
Updated Q1 symbol association from  to /1fdfaaef-d5fc-4743-9012-a247d9596129.
Updated Q1 fields.
Updated Q1 sheetname to '/'.
Updated Q1 sheetfile to 'Solar Project.kicad_sch'.
Updated Q1 footprint filters to 'Q_*'.
Connected Q1 pin 2 to PWR_NEG.
Add net Net-(Q1-G).
Connected Q1 pin 1 to Net-(Q1-G).
Add net Net-(Q1-D).
Connected Q1 pin 3 to Net-(Q1-D).
Added Q2 (footprint 'PCM_JLCPCB:Q_SOT-23').
Changed REF** reference designator to Q2.
Changed Q2 value from SOT-23 to BSS138.
Updated Q2 symbol association from  to /57b83498-62f0-4dc9-a850-e345d63e31aa.
Updated Q2 fields.
Updated Q2 sheetname to '/'.
Updated Q2 sheetfile to 'Solar Project.kicad_sch'.
Updated Q2 footprint filters to 'Q_*'.
Add net Net-(Q2-G).
Connected Q2 pin 1 to Net-(Q2-G).
Add net Net-(Q2-D).
Connected Q2 pin 3 to Net-(Q2-D).
Connected Q2 pin 2 to PWR_NEG.
Added R1 (footprint 'PCM_JLCPCB:R_0805').
Changed REF** reference designator to R1.
Changed R1 value from R_0805_2012Metric to 5.1kΩ.
Updated R1 symbol association from  to /bb8df506-27af-4225-9b6e-d3fdfedcc277.
Updated R1 fields.
Updated R1 sheetname to '/'.
Updated R1 sheetfile to 'Solar Project.kicad_sch'.
Updated R1 footprint filters to 'R_*'.
Connected R1 pin 2 to Net-(J5-CC1).
Connected R1 pin 1 to PWR_NEG.
Added R2 (footprint 'PCM_JLCPCB:R_0805').
Changed REF** reference designator to R2.
Changed R2 value from R_0805_2012Metric to 10Ω.
Updated R2 symbol association from  to /5aedc350-9e65-4d78-acfd-e2399e791510.
Updated R2 fields.
Updated R2 sheetname to '/'.
Updated R2 sheetfile to 'Solar Project.kicad_sch'.
Updated R2 footprint filters to 'R_*'.
Connected R2 pin 2 to Net-(Q1-D).
Connected R2 pin 1 to Net-(U5-G1).
Added R3 (footprint 'PCM_JLCPCB:R_0805').
Changed REF** reference designator to R3.
Changed R3 value from R_0805_2012Metric to 66.5k.
Updated R3 symbol association from  to /f3fc6b1b-2dd8-41f3-b4a0-cb8737ab2dc4.
Updated R3 fields.
Updated R3 sheetname to '/'.
Updated R3 sheetfile to 'Solar Project.kicad_sch'.
Updated R3 footprint filters to 'R_*'.
Connected R3 pin 1 to V_out.
Add net _OUTPUT Feedback.
Connected R3 pin 2 to _OUTPUT Feedback.
Added R4 (footprint 'PCM_JLCPCB:R_0805').
Changed REF** reference designator to R4.
Changed R4 value from R_0805_2012Metric to 5.1kΩ.
Updated R4 symbol association from  to /f0e9e9bf-5be8-49ee-8255-9fa9b8195a1b.
Updated R4 fields.
Updated R4 sheetname to '/'.
Updated R4 sheetfile to 'Solar Project.kicad_sch'.
Updated R4 footprint filters to 'R_*'.
Connected R4 pin 2 to Net-(J5-CC2).
Connected R4 pin 1 to PWR_NEG.
Added R5 (footprint 'PCM_JLCPCB:R_0805').
Changed REF** reference designator to R5.
Changed R5 value from R_0805_2012Metric to 4.7kΩ.
Updated R5 symbol association from  to /229b15b6-c9a1-4602-835a-d2baeb86179e.
Updated R5 fields.
Updated R5 sheetname to '/'.
Updated R5 sheetfile to 'Solar Project.kicad_sch'.
Updated R5 footprint filters to 'R_*'.
Add net Net-(U3-RST#).
Connected R5 pin 1 to Net-(U3-RST#).
Connected R5 pin 2 to CTRL_3V3.
Added R6 (footprint 'PCM_JLCPCB:R_0805').
Changed REF** reference designator to R6.
Changed R6 value from R_0805_2012Metric to 22kΩ.
Updated R6 symbol association from  to /c10de21d-4e35-4ab0-b290-1683e13467f7.
Updated R6 fields.
Updated R6 sheetname to '/'.
Updated R6 sheetfile to 'Solar Project.kicad_sch'.
Updated R6 footprint filters to 'R_*'.
Connected R6 pin 2 to Net-(U4-FB).
Add net Net-(R11-Pad2).
Connected R6 pin 1 to Net-(R11-Pad2).
Added R7 (footprint 'PCM_JLCPCB:R_0805').
Changed REF** reference designator to R7.
Changed R7 value from R_0805_2012Metric to 430k.
Updated R7 symbol association from  to /d09dd48d-8586-45c9-9a25-d6f021c7ed5f.
Updated R7 fields.
Updated R7 sheetname to '/'.
Updated R7 sheetfile to 'Solar Project.kicad_sch'.
Updated R7 footprint filters to 'R_*'.
Add net Net-(R10-Pad1).
Connected R7 pin 2 to Net-(R10-Pad1).
Connected R7 pin 1 to Net-(U4-FB).
Added R8 (footprint 'PCM_JLCPCB:R_0805').
Changed REF** reference designator to R8.
Changed R8 value from R_0805_2012Metric to 27kΩ.
Updated R8 symbol association from  to /aedb0edf-224f-439e-8a21-cc26faeebce8.
Updated R8 fields.
Updated R8 sheetname to '/'.
Updated R8 sheetfile to 'Solar Project.kicad_sch'.
Updated R8 footprint filters to 'R_*'.
Connected R8 pin 2 to PWR_NEG.
Add net Net-(U4-RON).
Connected R8 pin 1 to Net-(U4-RON).
Added R9 (footprint 'PCM_JLCPCB:R_0805').
Changed REF** reference designator to R9.
Changed R9 value from R_0805_2012Metric to 180k.
Updated R9 symbol association from  to /739ab897-c4dd-43b8-a7ca-178a39536ccf.
Updated R9 fields.
Updated R9 sheetname to '/'.
Updated R9 sheetfile to 'Solar Project.kicad_sch'.
Updated R9 footprint filters to 'R_*'.
Connected R9 pin 2 to Net-(U4-SW).
Add net Net-(R12-Pad1).
Connected R9 pin 1 to Net-(R12-Pad1).
Added R10 (footprint 'PCM_JLCPCB:R_0805').
Changed REF** reference designator to R10.
Changed R10 value from R_0805_2012Metric to 22kΩ.
Updated R10 symbol association from  to /cfaa8063-5a61-408d-a150-57d8c3cdf9db.
Updated R10 fields.
Updated R10 sheetname to '/'.
Updated R10 sheetfile to 'Solar Project.kicad_sch'.
Updated R10 footprint filters to 'R_*'.
Connected R10 pin 2 to CTRL_3V3.
Connected R10 pin 1 to Net-(R10-Pad1).
Added R11 (footprint 'PCM_JLCPCB:R_0805').
Changed REF** reference designator to R11.
Changed R11 value from R_0805_2012Metric to 240k.
Updated R11 symbol association from  to /0ed40b3c-696e-4fad-a552-153df93dee90.
Updated R11 fields.
Updated R11 sheetname to '/'.
Updated R11 sheetfile to 'Solar Project.kicad_sch'.
Updated R11 footprint filters to 'R_*'.
Connected R11 pin 1 to PWR_NEG.
Connected R11 pin 2 to Net-(R11-Pad2).
Added R12 (footprint 'PCM_JLCPCB:R_0805').
Changed REF** reference designator to R12.
Changed R12 value from R_0805_2012Metric to 6.8kΩ.
Updated R12 symbol association from  to /f65093b3-639f-457c-9107-9c8088b6428d.
Updated R12 fields.
Updated R12 sheetname to '/'.
Updated R12 sheetfile to 'Solar Project.kicad_sch'.
Updated R12 footprint filters to 'R_*'.
Connected R12 pin 2 to Net-(C10-Pad1).
Connected R12 pin 1 to Net-(R12-Pad1).
Added R13 (footprint 'PCM_JLCPCB:R_0805').
Changed REF** reference designator to R13.
Changed R13 value from R_0805_2012Metric to 1MΩ.
Updated R13 symbol association from  to /fc084ca8-da5d-4ba6-be98-d0c3cac79101.
Updated R13 fields.
Updated R13 sheetname to '/'.
Updated R13 sheetfile to 'Solar Project.kicad_sch'.
Updated R13 footprint filters to 'R_*'.
Connected R13 pin 1 to Net-(U4-VIN).
Add net Net-(U4-EN/UVLO).
Connected R13 pin 2 to Net-(U4-EN/UVLO).
Added R14 (footprint 'PCM_JLCPCB:R_0805').
Changed REF** reference designator to R14.
Changed R14 value from R_0805_2012Metric to 330kΩ.
Updated R14 symbol association from  to /7ff63818-9beb-489f-9592-6da7e7f0224f.
Updated R14 fields.
Updated R14 sheetname to '/'.
Updated R14 sheetfile to 'Solar Project.kicad_sch'.
Updated R14 footprint filters to 'R_*'.
Connected R14 pin 1 to Net-(U4-EN/UVLO).
Add net Net-(R14-Pad2).
Connected R14 pin 2 to Net-(R14-Pad2).
Added R15 (footprint 'PCM_JLCPCB:R_0805').
Changed REF** reference designator to R15.
Changed R15 value from R_0805_2012Metric to 2kΩ.
Updated R15 symbol association from  to /090310f5-cbee-4be6-83ac-887a4886cac3.
Updated R15 fields.
Updated R15 sheetname to '/'.
Updated R15 sheetfile to 'Solar Project.kicad_sch'.
Updated R15 footprint filters to 'R_*'.
Connected R15 pin 2 to PWR_NEG.
Connected R15 pin 1 to Net-(R14-Pad2).
Added R16 (footprint 'Resistor_SMD:R_2512_6332Metric').
Changed REF** reference designator to R16.
Changed R16 value from R_2512_6332Metric to 0.001ohms.
Updated R16 symbol association from  to /34caffd0-d144-4066-9d7d-90a77dc98a02.
Updated R16 fields.
Updated R16 sheetname to '/'.
Updated R16 sheetfile to 'Solar Project.kicad_sch'.
Updated R16 footprint filters to 'R_*Shunt*'.
Add net ISNSN.
Connected R16 pin 2 to ISNSN.
Add net Net-(R16-Pad1).
Connected R16 pin 1 to Net-(R16-Pad1).
Added R17 (footprint 'PCM_JLCPCB:R_0805').
Changed REF** reference designator to R17.
Changed R17 value from R_0805_2012Metric to 5.62k.
Updated R17 symbol association from  to /c2fd093a-b715-4b05-9b91-2adf50b48aa7.
Updated R17 fields.
Updated R17 sheetname to '/'.
Updated R17 sheetfile to 'Solar Project.kicad_sch'.
Updated R17 footprint filters to 'R_*'.
Connected R17 pin 2 to PWR_NEG.
Add net V_in_FB.
Connected R17 pin 1 to V_in_FB.
Added R18 (footprint 'PCM_JLCPCB:R_0805').
Changed REF** reference designator to R18.
Changed R18 value from R_0805_2012Metric to 66.5k.
Updated R18 symbol association from  to /cdc5a8eb-6b40-4aeb-ba17-ad78418b98fc.
Updated R18 fields.
Updated R18 sheetname to '/'.
Updated R18 sheetfile to 'Solar Project.kicad_sch'.
Updated R18 footprint filters to 'R_*'.
Connected R18 pin 1 to PV_IN_POS.
Connected R18 pin 2 to V_in_FB.
Added R19 (footprint 'PCM_JLCPCB:R_0805').
Changed REF** reference designator to R19.
Changed R19 value from R_0805_2012Metric to 10kΩ.
Updated R19 symbol association from  to /08725dac-d658-4ac5-b312-7a0f55d91a0e.
Updated R19 fields.
Updated R19 sheetname to '/'.
Updated R19 sheetfile to 'Solar Project.kicad_sch'.
Updated R19 footprint filters to 'R_*'.
Connected R19 pin 1 to CTRL_3V3.
Add net FAULT_OVP.
Connected R19 pin 2 to FAULT_OVP.
Added R20 (footprint 'PCM_JLCPCB:R_0805').
Changed REF** reference designator to R20.
Changed R20 value from R_0805_2012Metric to 499kΩ.
Updated R20 symbol association from  to /948d2aec-760b-4dc4-acd0-591f9f35c7f7.
Updated R20 fields.
Updated R20 sheetname to '/'.
Updated R20 sheetfile to 'Solar Project.kicad_sch'.
Updated R20 footprint filters to 'R_*'.
Add net OVP_SENSE.
Connected R20 pin 2 to OVP_SENSE.
Connected R20 pin 1 to BAT_BUS_POS.
Added R21 (footprint 'PCM_JLCPCB:R_0805').
Changed REF** reference designator to R21.
Changed R21 value from R_0805_2012Metric to 102k.
Updated R21 symbol association from  to /a4c90a32-9c98-49c3-8643-e7f97d9369a0.
Updated R21 fields.
Updated R21 sheetname to '/'.
Updated R21 sheetfile to 'Solar Project.kicad_sch'.
Updated R21 footprint filters to 'R_*'.
Connected R21 pin 1 to CTRL_3V3.
Add net OVP_REF.
Connected R21 pin 2 to OVP_REF.
Added R22 (footprint 'Resistor_SMD:R_2512_6332Metric').
Changed REF** reference designator to R22.
Changed R22 value from R_2512_6332Metric to 0.001ohms.
Updated R22 symbol association from  to /acfe2c80-2498-4c82-aca3-320a1d0f2cae.
Updated R22 fields.
Updated R22 sheetname to '/'.
Updated R22 sheetfile to 'Solar Project.kicad_sch'.
Updated R22 footprint filters to 'R_*Shunt*'.
Connected R22 pin 1 to Net-(L2-Pad1).
Add net _CSB_2.
Connected R22 pin 2 to _CSB_2.
Added R23 (footprint 'PCM_JLCPCB:R_0805').
Changed REF** reference designator to R23.
Changed R23 value from R_0805_2012Metric to 75kΩ.
Updated R23 symbol association from  to /3d8e001b-17dc-4a59-866b-6953e990a3d7.
Updated R23 fields.
Updated R23 sheetname to '/'.
Updated R23 sheetfile to 'Solar Project.kicad_sch'.
Updated R23 footprint filters to 'R_*'.
Connected R23 pin 1 to PV_IN_POS.
Add net _Undervoltage Feedback.
Connected R23 pin 2 to _Undervoltage Feedback.
Added R25 (footprint 'PCM_JLCPCB:R_0805').
Changed REF** reference designator to R25.
Changed R25 value from R_0805_2012Metric to 5.62k.
Updated R25 symbol association from  to /fe69288b-21eb-43d1-a97f-562a14eb5bbb.
Updated R25 fields.
Updated R25 sheetname to '/'.
Updated R25 sheetfile to 'Solar Project.kicad_sch'.
Updated R25 footprint filters to 'R_*'.
Connected R25 pin 1 to _OUTPUT Feedback.
Connected R25 pin 2 to PWR_NEG.
Added R26 (footprint 'PCM_JLCPCB:R_0805').
Changed REF** reference designator to R26.
Changed R26 value from R_0805_2012Metric to 10Ω.
Updated R26 symbol association from  to /7db06b1e-d4a5-4466-821e-05b6f56a5bcf.
Updated R26 fields.
Updated R26 sheetname to '/'.
Updated R26 sheetfile to 'Solar Project.kicad_sch'.
Updated R26 footprint filters to 'R_*'.
Add net _CSA_2.
Connected R26 pin 1 to _CSA_2.
Connected R26 pin 2 to Net-(U6-CSA).
Added R27 (footprint 'PCM_JLCPCB:R_0805').
Changed REF** reference designator to R27.
Changed R27 value from R_0805_2012Metric to 10Ω.
Updated R27 symbol association from  to /7cb151ad-3662-4fc6-b077-fd6811f47d0a.
Updated R27 fields.
Updated R27 sheetname to '/'.
Updated R27 sheetfile to 'Solar Project.kicad_sch'.
Updated R27 footprint filters to 'R_*'.
Connected R27 pin 1 to _CSB_2.
Connected R27 pin 2 to Net-(U6-CSB).
Added R28 (footprint 'PCM_JLCPCB:R_0603').
Changed REF** reference designator to R28.
Changed R28 value from R_0603_1608Metric to 51.7k.
Updated R28 symbol association from  to /2ddf2800-dcf5-46c2-89d0-84e4595b7332.
Updated R28 fields.
Updated R28 sheetname to '/'.
Updated R28 sheetfile to 'Solar Project.kicad_sch'.
Updated R28 footprint filters to 'R_*'.
Add net Net-(U6-RT).
Connected R28 pin 1 to Net-(U6-RT).
Connected R28 pin 2 to PGND.
Added R29 (footprint 'PCM_JLCPCB:R_0805').
Changed REF** reference designator to R29.
Changed R29 value from R_0805_2012Metric to 20.5k.
Updated R29 symbol association from  to /879bf51b-854c-4944-8bac-15836514ab25.
Updated R29 fields.
Updated R29 sheetname to '/'.
Updated R29 sheetfile to 'Solar Project.kicad_sch'.
Updated R29 footprint filters to 'R_*'.
Add net Net-(U6-CFG2).
Connected R29 pin 1 to Net-(U6-CFG2).
Connected R29 pin 2 to PGND.
Added R30 (footprint 'PCM_JLCPCB:R_0805').
Changed REF** reference designator to R30.
Changed R30 value from R_0805_2012Metric to 40.2k.
Updated R30 symbol association from  to /21e1f8f8-2289-4efa-9936-7296e027d6d5.
Updated R30 fields.
Updated R30 sheetname to '/'.
Updated R30 sheetfile to 'Solar Project.kicad_sch'.
Updated R30 footprint filters to 'R_*'.
Add net Net-(U6-CDC).
Connected R30 pin 1 to Net-(U6-CDC).
Connected R30 pin 2 to PGND.
Added R31 (footprint 'PCM_JLCPCB:R_0805').
Changed REF** reference designator to R31.
Changed R31 value from R_0805_2012Metric to 2.43K.
Updated R31 symbol association from  to /a50f0a67-923e-4be0-b5df-8720e2fb4e78.
Updated R31 fields.
Updated R31 sheetname to '/'.
Updated R31 sheetfile to 'Solar Project.kicad_sch'.
Updated R31 footprint filters to 'R_*'.
Connected R31 pin 2 to PGND.
Connected R31 pin 1 to Net-(C24-Pad1).
Added R32 (footprint 'PCM_JLCPCB:R_0805').
Changed REF** reference designator to R32.
Changed R32 value from R_0805_2012Metric to 100kΩ.
Updated R32 symbol association from  to /c4e558da-9609-4fe6-b34a-4ed7c3db4f81.
Updated R32 fields.
Updated R32 sheetname to '/'.
Updated R32 sheetfile to 'Solar Project.kicad_sch'.
Updated R32 footprint filters to 'R_*'.
Add net Net-(U6-ILIMCOMP_ISET).
Connected R32 pin 1 to Net-(U6-ILIMCOMP_ISET).
Connected R32 pin 2 to PWR_NEG.
Added R33 (footprint 'PCM_JLCPCB:R_0805').
Changed REF** reference designator to R33.
Changed R33 value from R_0805_2012Metric to 6.49k.
Updated R33 symbol association from  to /28e3a543-2b23-414d-8c18-f656d6c9987b.
Updated R33 fields.
Updated R33 sheetname to '/'.
Updated R33 sheetfile to 'Solar Project.kicad_sch'.
Updated R33 footprint filters to 'R_*'.
Connected R33 pin 2 to PGND.
Add net Net-(U6-ADDR_SLOPE_CFG1).
Connected R33 pin 1 to Net-(U6-ADDR_SLOPE_CFG1).
Added R34 (footprint 'PCM_JLCPCB:R_0805').
Changed REF** reference designator to R34.
Changed R34 value from R_0805_2012Metric to 10kΩ.
Updated R34 symbol association from  to /651c72f3-5b4c-4974-a3cf-9632ec140484.
Updated R34 fields.
Updated R34 sheetname to '/'.
Updated R34 sheetfile to 'Solar Project.kicad_sch'.
Updated R34 footprint filters to 'R_*'.
Add net U6_FLT.
Connected R34 pin 1 to U6_FLT.
Connected R34 pin 2 to CTRL_3V3.
Added R35 (footprint 'PCM_JLCPCB:R_0805').
Changed REF** reference designator to R35.
Changed R35 value from R_0805_2012Metric to 180kΩ.
Updated R35 symbol association from  to /ba38d3a3-86e7-402b-baff-93e538b86272.
Updated R35 fields.
Updated R35 sheetname to '/'.
Updated R35 sheetfile to 'Solar Project.kicad_sch'.
Updated R35 footprint filters to 'R_*'.
Add net V_in_ADC.
Connected R35 pin 2 to V_in_ADC.
Connected R35 pin 1 to /PV_IN_POS_FUSED.
Added R36 (footprint 'PCM_JLCPCB:R_0805').
Changed REF** reference designator to R36.
Changed R36 value from R_0805_2012Metric to 10kΩ.
Updated R36 symbol association from  to /71a4cd61-ff04-4d00-b20d-1f84aa2745a1.
Updated R36 fields.
Updated R36 sheetname to '/'.
Updated R36 sheetfile to 'Solar Project.kicad_sch'.
Updated R36 footprint filters to 'R_*'.
Connected R36 pin 1 to V_in_ADC.
Connected R36 pin 2 to PWR_NEG.
Added R37 (footprint 'PCM_JLCPCB:R_0805').
Changed REF** reference designator to R37.
Changed R37 value from R_0805_2012Metric to 100kΩ.
Updated R37 symbol association from  to /b816a656-7489-45d6-b805-ad1bb7ecedd9.
Updated R37 fields.
Updated R37 sheetname to '/'.
Updated R37 sheetfile to 'Solar Project.kicad_sch'.
Updated R37 footprint filters to 'R_*'.
Connected R37 pin 1 to CTRL_3V3.
Connected R37 pin 2 to Net-(Q1-G).
Added R38 (footprint 'PCM_JLCPCB:R_0805').
Changed REF** reference designator to R38.
Changed R38 value from R_0805_2012Metric to 100kΩ.
Updated R38 symbol association from  to /b789ab44-6dd2-46a7-abfe-fe3acbea1aec.
Updated R38 fields.
Updated R38 sheetname to '/'.
Updated R38 sheetfile to 'Solar Project.kicad_sch'.
Updated R38 footprint filters to 'R_*'.
Connected R38 pin 2 to Net-(Q1-D).
Connected R38 pin 1 to Net-(R16-Pad1).
Added R39 (footprint 'PCM_JLCPCB:R_0805').
Changed REF** reference designator to R39.
Changed R39 value from R_0805_2012Metric to 10Ω.
Updated R39 symbol association from  to /06749d60-72fe-421d-b433-2c515f9d8fc9.
Updated R39 fields.
Updated R39 sheetname to '/'.
Updated R39 sheetfile to 'Solar Project.kicad_sch'.
Updated R39 footprint filters to 'R_*'.
Add net V_out _on.
Connected R39 pin 1 to V_out _on.
Connected R39 pin 2 to Net-(Q1-G).
Added R40 (footprint 'PCM_JLCPCB:R_0805').
Changed REF** reference designator to R40.
Changed R40 value from R_0805_2012Metric to 100kΩ.
Updated R40 symbol association from  to /e009ead2-0a79-44fd-9980-e7c53cbfcd1e.
Updated R40 fields.
Updated R40 sheetname to '/'.
Updated R40 sheetfile to 'Solar Project.kicad_sch'.
Updated R40 footprint filters to 'R_*'.
Connected R40 pin 2 to Net-(Q2-G).
Connected R40 pin 1 to CTRL_3V3.
Added R41 (footprint 'PCM_JLCPCB:R_0805').
Changed REF** reference designator to R41.
Changed R41 value from R_0805_2012Metric to 10Ω.
Updated R41 symbol association from  to /2c5c5ece-6b2b-4722-9bb5-6dbcab97b0b4.
Updated R41 fields.
Updated R41 sheetname to '/'.
Updated R41 sheetfile to 'Solar Project.kicad_sch'.
Updated R41 footprint filters to 'R_*'.
Connected R41 pin 2 to Net-(Q2-G).
Add net V_in_ON.
Connected R41 pin 1 to V_in_ON.
Added R42 (footprint 'PCM_JLCPCB:R_0805').
Changed REF** reference designator to R42.
Changed R42 value from R_0805_2012Metric to 10Ω.
Updated R42 symbol association from  to /0bfac9ad-7855-4264-ad01-c8af326a134c.
Updated R42 fields.
Updated R42 sheetname to '/'.
Updated R42 sheetfile to 'Solar Project.kicad_sch'.
Updated R42 footprint filters to 'R_*'.
Connected R42 pin 2 to Net-(U2-G1).
Connected R42 pin 1 to Net-(Q2-D).
Added R43 (footprint 'PCM_JLCPCB:R_0805').
Changed REF** reference designator to R43.
Changed R43 value from R_0805_2012Metric to 100kΩ.
Updated R43 symbol association from  to /735f9746-9e9c-4a83-8e98-cf5dd023575f.
Updated R43 fields.
Updated R43 sheetname to '/'.
Updated R43 sheetfile to 'Solar Project.kicad_sch'.
Updated R43 footprint filters to 'R_*'.
Connected R43 pin 1 to /PV_IN_POS_FUSED.
Connected R43 pin 2 to Net-(Q2-D).
Added R44 (footprint 'PCM_JLCPCB:R_0805').
Changed REF** reference designator to R44.
Changed R44 value from R_0805_2012Metric to 4.7kΩ.
Updated R44 symbol association from  to /c958dc51-529c-4457-b61e-60e7799a681d.
Updated R44 fields.
Updated R44 sheetname to '/'.
Updated R44 sheetfile to 'Solar Project.kicad_sch'.
Updated R44 footprint filters to 'R_*'.
Add net I2C CLK.
Connected R44 pin 1 to I2C CLK.
Connected R44 pin 2 to CTRL_3V3.
Added C1 (footprint 'PCM_JLCPCB:C_0805').
Added R45 (footprint 'PCM_JLCPCB:R_0805').
Changed REF** reference designator to R45.
Changed R45 value from R_0805_2012Metric to 4.7kΩ.
Updated R45 symbol association from  to /4917f94b-2d0a-4815-b70c-78c3049907e7.
Updated R45 fields.
Updated R45 sheetname to '/'.
Updated R45 sheetfile to 'Solar Project.kicad_sch'.
Updated R45 footprint filters to 'R_*'.
Add net I2C DATA.
Connected R45 pin 1 to I2C DATA.
Connected R45 pin 2 to CTRL_3V3.
Changed REF** reference designator to C1.
Added R46 (footprint 'PCM_JLCPCB:R_0805').
Changed REF** reference designator to R46.
Changed R46 value from R_0805_2012Metric to 330Ω.
Updated R46 symbol association from  to /bac2e02d-8ee8-4271-a241-46a686e8359c.
Updated R46 fields.
Updated R46 sheetname to '/'.
Updated R46 sheetfile to 'Solar Project.kicad_sch'.
Updated R46 footprint filters to 'R_*'.
Connected R46 pin 2 to Net-(D9-Pad2).
Connected R46 pin 1 to CTRL_3V3.
Changed C1 value from C_0805_2012Metric to 100nF.
Added R47 (footprint 'PCM_JLCPCB:R_0805').
Changed REF** reference designator to R47.
Changed R47 value from R_0805_2012Metric to 10kΩ.
Updated R47 symbol association from  to /d83c4e3e-1379-48dd-b954-4085b2ed419d.
Updated R47 fields.
Updated R47 sheetname to '/'.
Updated R47 sheetfile to 'Solar Project.kicad_sch'.
Updated R47 footprint filters to 'R_*'.
Connected R47 pin 2 to PWR_NEG.
Connected R47 pin 1 to OVP_SENSE.
Updated C1 symbol association from  to /de776bbb-a28a-443f-9fe9-b27ff8d27891.
Added R48 (footprint 'PCM_JLCPCB:R_0805').
Changed REF** reference designator to R48.
Changed R48 value from R_0805_2012Metric to 10kΩ.
Updated R48 symbol association from  to /5681c943-3e7b-47d9-902c-819652046af1.
Updated R48 fields.
Updated R48 sheetname to '/'.
Updated R48 sheetfile to 'Solar Project.kicad_sch'.
Updated R48 footprint filters to 'R_*'.
Connected R48 pin 2 to PWR_NEG.
Connected R48 pin 1 to OVP_REF.
Updated C1 fields.
Added R49 (footprint 'PCM_JLCPCB:R_0805').
Changed REF** reference designator to R49.
Changed R49 value from R_0805_2012Metric to 0Ω.
Updated R49 symbol association from  to /72bf907b-0c75-40c9-8187-b4ed7c59fcbf.
Updated R49 fields.
Updated R49 sheetname to '/'.
Updated R49 sheetfile to 'Solar Project.kicad_sch'.
Updated R49 footprint filters to 'R_*'.
Add net OCP_SENSE.
Connected R49 pin 2 to OCP_SENSE.
Add net OCP_MEAS.
Connected R49 pin 1 to OCP_MEAS.
Updated C1 sheetname to '/'.
Added R50 (footprint 'PCM_JLCPCB:R_0805').
Changed REF** reference designator to R50.
Changed R50 value from R_0805_2012Metric to 10kΩ.
Updated R50 symbol association from  to /ff9e7e87-175b-4612-9d5c-8f0e7afca692.
Updated R50 fields.
Updated R50 sheetname to '/'.
Updated R50 sheetfile to 'Solar Project.kicad_sch'.
Updated R50 footprint filters to 'R_*'.
Added R50 'Do not place' fabrication attribute.
Connected R50 pin 2 to PWR_NEG.
Connected R50 pin 1 to OCP_SENSE.
Updated C1 sheetfile to 'Solar Project.kicad_sch'.
Added R51 (footprint 'PCM_JLCPCB:R_0805').
Changed REF** reference designator to R51.
Changed R51 value from R_0805_2012Metric to 2.7kΩ.
Updated R51 symbol association from  to /91fdcceb-0328-4664-b7df-cf19d717987d.
Updated R51 fields.
Updated R51 sheetname to '/'.
Updated R51 sheetfile to 'Solar Project.kicad_sch'.
Updated R51 footprint filters to 'R_*'.
Connected R51 pin 1 to CTRL_3V3.
Add net OCP_REF.
Connected R51 pin 2 to OCP_REF.
Updated C1 footprint filters to 'C_*'.
Added R52 (footprint 'PCM_JLCPCB:R_0805').
Changed REF** reference designator to R52.
Changed R52 value from R_0805_2012Metric to 1kΩ.
Updated R52 symbol association from  to /c41e2211-d0f2-44ed-9c09-5383a72bb936.
Updated R52 fields.
Updated R52 sheetname to '/'.
Updated R52 sheetfile to 'Solar Project.kicad_sch'.
Updated R52 footprint filters to 'R_*'.
Connected R52 pin 2 to PWR_NEG.
Connected R52 pin 1 to OCP_REF.
Add net PWR_NEG.
Added R53 (footprint 'PCM_JLCPCB:R_0805').
Changed REF** reference designator to R53.
Changed R53 value from R_0805_2012Metric to 10kΩ.
Updated R53 symbol association from  to /f44aeff8-46bf-4c54-a38b-7ed1043d178b.
Updated R53 fields.
Updated R53 sheetname to '/'.
Updated R53 sheetfile to 'Solar Project.kicad_sch'.
Updated R53 footprint filters to 'R_*'.
Connected R53 pin 1 to CTRL_3V3.
Add net FAULT_OCP.
Connected R53 pin 2 to FAULT_OCP.
Connected C1 pin 2 to PWR_NEG.
Added R54 (footprint 'PCM_JLCPCB:R_0805').
Changed REF** reference designator to R54.
Changed R54 value from R_0805_2012Metric to 10kΩ.
Updated R54 symbol association from  to /9ee35227-8f2a-4334-9a80-fac47d5a07da.
Updated R54 fields.
Updated R54 sheetname to '/'.
Updated R54 sheetfile to 'Solar Project.kicad_sch'.
Updated R54 footprint filters to 'R_*'.
Connected R54 pin 1 to CTRL_3V3.
Add net Net-(SW1-B).
Connected R54 pin 2 to Net-(SW1-B).
Add net VBUS.
Added R55 (footprint 'PCM_JLCPCB:R_0805').
Changed REF** reference designator to R55.
Changed R55 value from R_0805_2012Metric to 10kΩ.
Updated R55 symbol association from  to /b7e5dfd3-baf7-41fc-8532-3fde89a2fa2d.
Updated R55 fields.
Updated R55 sheetname to '/'.
Updated R55 sheetfile to 'Solar Project.kicad_sch'.
Updated R55 footprint filters to 'R_*'.
Connected R55 pin 1 to CTRL_3V3.
Add net Net-(SW2-B).
Connected R55 pin 2 to Net-(SW2-B).
Connected C1 pin 1 to VBUS.
Added R56 (footprint 'PCM_JLCPCB:R_0805').
Changed REF** reference designator to R56.
Changed R56 value from R_0805_2012Metric to 10kΩ.
Updated R56 symbol association from  to /6ce76b45-cb3a-4c38-a04d-58e54fef972c.
Updated R56 fields.
Updated R56 sheetname to '/'.
Updated R56 sheetfile to 'Solar Project.kicad_sch'.
Updated R56 footprint filters to 'R_*'.
Add net Net-(SW3-B).
Connected R56 pin 2 to Net-(SW3-B).
Connected R56 pin 1 to CTRL_3V3.
Added C2 (footprint 'PCM_JLCPCB:C_0805').
Added R57 (footprint 'PCM_JLCPCB:R_0805').
Changed REF** reference designator to R57.
Changed R57 value from R_0805_2012Metric to 10kΩ.
Updated R57 symbol association from  to /43e09f09-4e5f-4a1f-b323-222897344b17.
Updated R57 fields.
Updated R57 sheetname to '/'.
Updated R57 sheetfile to 'Solar Project.kicad_sch'.
Updated R57 footprint filters to 'R_*'.
Add net Net-(SW4-B).
Connected R57 pin 2 to Net-(SW4-B).
Connected R57 pin 1 to CTRL_3V3.
Changed REF** reference designator to C2.
Added R58 (footprint 'PCM_JLCPCB:R_0805').
Changed REF** reference designator to R58.
Changed R58 value from R_0805_2012Metric to 10kΩ.
Updated R58 symbol association from  to /912efa90-0c17-40fe-ad6a-7b6832ca79a1.
Updated R58 fields.
Updated R58 sheetname to '/'.
Updated R58 sheetfile to 'Solar Project.kicad_sch'.
Updated R58 footprint filters to 'R_*'.
Add net Net-(SW5-B).
Connected R58 pin 2 to Net-(SW5-B).
Connected R58 pin 1 to CTRL_3V3.
Changed C2 value from C_0805_2012Metric to 1uF.
Added R59 (footprint 'PCM_JLCPCB:R_0805').
Changed REF** reference designator to R59.
Changed R59 value from R_0805_2012Metric to 10kΩ.
Updated R59 symbol association from  to /2d230193-9465-4ea7-bb0d-df98369757c6.
Updated R59 fields.
Updated R59 sheetname to '/'.
Updated R59 sheetfile to 'Solar Project.kicad_sch'.
Updated R59 footprint filters to 'R_*'.
Connected R59 pin 2 to Net-(S1-A).
Connected R59 pin 1 to CTRL_3V3.
Updated C2 symbol association from  to /01eb3a9e-dc94-4a77-9e0a-a55e9cfaa504.
Added R60 (footprint 'PCM_JLCPCB:R_0805').
Changed REF** reference designator to R60.
Changed R60 value from R_0805_2012Metric to 1.5kΩ.
Updated R60 symbol association from  to /af5a1532-b34d-47fa-9a17-f00376713007.
Updated R60 fields.
Updated R60 sheetname to '/'.
Updated R60 sheetfile to 'Solar Project.kicad_sch'.
Updated R60 footprint filters to 'R_*'.
Add net Net-(R60-Pad1).
Connected R60 pin 1 to Net-(R60-Pad1).
Connected R60 pin 2 to PWR_NEG.
Updated C2 fields.
Added R61 (footprint 'PCM_JLCPCB:R_0805').
Changed REF** reference designator to R61.
Changed R61 value from R_0805_2012Metric to 20kΩ.
Updated R61 symbol association from  to /e0f7b85b-73fa-4126-b944-bd954f0f00ad.
Updated C2 sheetname to '/'.
Updated R61 sheetname to '/'.
Updated R61 sheetfile to 'Solar Project.kicad_sch'.
Updated R61 footprint filters to 'R_*'.
Connected R61 pin 1 to _Undervoltage Feedback.
Connected R61 pin 2 to Net-(R60-Pad1).
Updated C2 sheetfile to 'Solar Project.kicad_sch'.
Added S1 (footprint 'PCM_JLCPCB:SW_TS-1088-AR02016').
Changed REF** reference designator to S1.
Changed S1 value from SW_TS-1088-AR02016 to Tactile Button, 160gf.
Updated S1 symbol association from  to /8bee250c-7bf1-4342-bac4-47428327969c.
Updated S1 fields.
Updated S1 sheetname to '/'.
Updated S1 sheetfile to 'Solar Project.kicad_sch'.
Connected S1 pin 1 to Net-(S1-A).
Connected S1 pin 2 to PWR_NEG.
Updated C2 footprint filters to 'C_*'.
Added SW1 (footprint 'PCM_JLCPCB:SW-SMD_4P-L5.1-W5.1-P3.70-LS6.5-TL-2').
Changed REF** reference designator to SW1.
Changed SW1 value from SW-SMD_4P-L5.1-W5.1-P3.70-LS6.5-TL-2 to Tactile Button, 160gf.
Updated SW1 symbol association from  to /3a6bd9a6-d7e2-4569-94ec-4f556934624d.
Updated SW1 fields.
Updated SW1 sheetname to '/'.
Updated SW1 sheetfile to 'Solar Project.kicad_sch'.
Connected SW1 pin 3 to PWR_NEG.
Connected SW1 pin 2 to Net-(SW1-B).
Connected SW1 pin 4 to PWR_NEG.
Add net BTN_UP_N.
Connected SW1 pin 1 to BTN_UP_N.
Connected C2 pin 1 to VBUS.
Added SW2 (footprint 'PCM_JLCPCB:SW-SMD_4P-L5.1-W5.1-P3.70-LS6.5-TL-2').
Changed REF** reference designator to SW2.
Changed SW2 value from SW-SMD_4P-L5.1-W5.1-P3.70-LS6.5-TL-2 to Tactile Button, 160gf.
Updated SW2 symbol association from  to /6dec21a5-f8fb-4586-91c0-592fef596007.
Updated SW2 fields.
Updated SW2 sheetname to '/'.
Updated SW2 sheetfile to 'Solar Project.kicad_sch'.
Connected SW2 pin 2 to Net-(SW2-B).
Connected SW2 pin 3 to PWR_NEG.
Add net BTN_DN_N.
Connected SW2 pin 1 to BTN_DN_N.
Connected SW2 pin 4 to PWR_NEG.
Connected C2 pin 2 to PWR_NEG.
Added SW3 (footprint 'PCM_JLCPCB:SW-SMD_4P-L5.1-W5.1-P3.70-LS6.5-TL-2').
Changed REF** reference designator to SW3.
Changed SW3 value from SW-SMD_4P-L5.1-W5.1-P3.70-LS6.5-TL-2 to Tactile Button, 160gf.
Updated SW3 symbol association from  to /2b7f3741-ef26-40e5-aee7-04233bf6775b.
Updated SW3 fields.
Updated SW3 sheetname to '/'.
Updated SW3 sheetfile to 'Solar Project.kicad_sch'.
Connected SW3 pin 3 to PWR_NEG.
Connected SW3 pin 2 to Net-(SW3-B).
Connected SW3 pin 4 to PWR_NEG.
Add net BTN_RT_N.
Connected SW3 pin 1 to BTN_RT_N.
Added C3 (footprint 'Capacitor_THT:CP_Radial_D6.3mm_P2.50mm').
Added SW4 (footprint 'PCM_JLCPCB:SW-SMD_4P-L5.1-W5.1-P3.70-LS6.5-TL-2').
Changed REF** reference designator to SW4.
Changed SW4 value from SW-SMD_4P-L5.1-W5.1-P3.70-LS6.5-TL-2 to Tactile Button, 160gf.
Updated SW4 symbol association from  to /971d89b9-18b0-4346-9662-5ab7e1eb7f92.
Updated SW4 fields.
Updated SW4 sheetname to '/'.
Updated SW4 sheetfile to 'Solar Project.kicad_sch'.
Connected SW4 pin 4 to PWR_NEG.
Add net BTN_LT_N.
Connected SW4 pin 1 to BTN_LT_N.
Connected SW4 pin 3 to PWR_NEG.
Connected SW4 pin 2 to Net-(SW4-B).
Changed REF** reference designator to C3.
Added SW5 (footprint 'PCM_JLCPCB:SW-SMD_4P-L5.1-W5.1-P3.70-LS6.5-TL-2').
Changed REF** reference designator to SW5.
Changed SW5 value from SW-SMD_4P-L5.1-W5.1-P3.70-LS6.5-TL-2 to Tactile Button, 160gf.
Updated SW5 symbol association from  to /a9f4bc47-af17-4b82-98a9-7fc0c8a6c045.
Updated SW5 fields.
Updated SW5 sheetname to '/'.
Updated SW5 sheetfile to 'Solar Project.kicad_sch'.
Add net BTN_ENT_N.
Connected SW5 pin 1 to BTN_ENT_N.
Connected SW5 pin 2 to Net-(SW5-B).
Connected SW5 pin 3 to PWR_NEG.
Connected SW5 pin 4 to PWR_NEG.
Changed C3 value from CP_Radial_D6.3mm_P2.50mm to 47uf.
Updated C3 symbol association from  to /f3c4e8ab-fe98-4205-b4c9-0df098d44499.
Added TP1 (footprint 'Connector_PinHeader_2.54mm:PinHeader_1x01_P2.54mm_Vertical').
Changed REF** reference designator to TP1.
Changed TP1 value from PinHeader_1x01_P2.54mm_Vertical to TestPoint_Small.
Updated TP1 symbol association from  to /9451a89d-a728-4213-9a4b-a7699d5eedb1.
Updated TP1 fields.
Updated TP1 sheetname to '/'.
Updated TP1 sheetfile to 'Solar Project.kicad_sch'.
Updated TP1 footprint filters to 'Pin* Test*'.
Connected TP1 pin 1 to Net-(R16-Pad1).
Updated C3 fields.
Added TP2 (footprint 'Connector_PinHeader_2.54mm:PinHeader_1x01_P2.54mm_Vertical').
Changed REF** reference designator to TP2.
Changed TP2 value from PinHeader_1x01_P2.54mm_Vertical to TestPoint_Small.
Updated TP2 symbol association from  to /be7369aa-6373-4a97-91d2-ae610ec46523.
Updated TP2 fields.
Updated TP2 sheetname to '/'.
Updated TP2 sheetfile to 'Solar Project.kicad_sch'.
Updated TP2 footprint filters to 'Pin* Test*'.
Connected TP2 pin 1 to CHG_OUT_POS.
Updated C3 sheetname to '/'.
Added TP3 (footprint 'Connector_PinHeader_2.54mm:PinHeader_1x01_P2.54mm_Vertical').
Changed REF** reference designator to TP3.
Changed TP3 value from PinHeader_1x01_P2.54mm_Vertical to TestPoint_Small.
Updated TP3 symbol association from  to /ef9930f4-acd7-458b-aa8c-cfba3dc81765.
Updated TP3 fields.
Updated TP3 sheetname to '/'.
Updated TP3 sheetfile to 'Solar Project.kicad_sch'.
Updated TP3 footprint filters to 'Pin* Test*'.
Connected TP3 pin 1 to V_out.
Updated C3 sheetfile to 'Solar Project.kicad_sch'.
Added TP4 (footprint 'Connector_PinHeader_2.54mm:PinHeader_1x01_P2.54mm_Vertical').
Changed REF** reference designator to TP4.
Changed TP4 value from PinHeader_1x01_P2.54mm_Vertical to TestPoint_Small.
Updated TP4 symbol association from  to /57d1ddef-52ca-4822-93d3-fdf797cd7144.
Updated TP4 fields.
Updated TP4 sheetname to '/'.
Updated TP4 sheetfile to 'Solar Project.kicad_sch'.
Updated TP4 footprint filters to 'Pin* Test*'.
Connected TP4 pin 1 to PV_IN_POS.
Updated C3 footprint filters to 'C_*'.
Added TP5 (footprint 'Connector_PinHeader_2.54mm:PinHeader_1x01_P2.54mm_Vertical').
Changed REF** reference designator to TP5.
Changed TP5 value from PinHeader_1x01_P2.54mm_Vertical to TestPoint_Small.
Updated TP5 symbol association from  to /ec005c79-2af7-40f0-b284-8be810656dd8.
Updated TP5 fields.
Updated TP5 sheetname to '/'.
Updated TP5 sheetfile to 'Solar Project.kicad_sch'.
Updated TP5 footprint filters to 'Pin* Test*'.
Connected TP5 pin 1 to PWR_NEG.
Connected C3 pin 2 to PWR_NEG.
Added U1 (footprint 'Package_DFN_QFN:QFN-48-1EP_6x6mm_P0.4mm_EP4.4x4.4mm_ThermalVias').
Changed REF** reference designator to U1.
Changed U1 value from QFN-48-1EP_6x6mm_P0.4mm_EP4.4x4.4mm_ThermalVias to STM32G431CBU6.
Updated U1 symbol association from  to /6c920233-fbb2-4c79-979c-c176cae6acb4.
Updated U1 fields.
Updated U1 sheetname to '/'.
Updated U1 sheetfile to 'Solar Project.kicad_sch'.
Add net unconnected-(U1-PB10-Pad22).
Connected U1 pin 22 to unconnected-(U1-PB10-Pad22).
Add net unconnected-(U1-PB13-Pad26).
Connected U1 pin 26 to unconnected-(U1-PB13-Pad26).
Add net unconnected-(U1-PA0-Pad8).
Connected U1 pin 8 to unconnected-(U1-PA0-Pad8).
Connected U1 pin 37 to SWCLK.
Connected U1 pin 38 to BTN_UP_N.
Connected U1 pin 48 to CTRL_3V3.
Connected U1 pin 18 to FAULT_OVP.
Connected U1 pin 49 to PWR_NEG.
Connected U1 pin 42 to BTN_LT_N.
Add net unconnected-(U1-PC10-Pad39).
Connected U1 pin 39 to unconnected-(U1-PC10-Pad39).
Connected U1 pin 49 to PWR_NEG.
Connected U1 pin 44 to I2C DATA.
Connected U1 pin 17 to FAULT_OCP.
Connected U1 pin 6 to Net-(U1-PF1-OSC_OUT).
Add net RXD.
Connected U1 pin 31 to RXD.
Add net CTS.
Connected U1 pin 33 to CTS.
Connected U1 pin 30 to V_out _on.
Connected U1 pin 49 to PWR_NEG.
Add net unconnected-(U1-PC4-Pad16).
Connected U1 pin 16 to unconnected-(U1-PC4-Pad16).
Connected U1 pin 49 to PWR_NEG.
Connected U1 pin 49 to PWR_NEG.
Add net RTS.
Connected U1 pin 34 to RTS.
Add net unconnected-(U1-PA7-Pad15).
Connected U1 pin 15 to unconnected-(U1-PA7-Pad15).
Add net unconnected-(U1-PC6-Pad29).
Connected U1 pin 29 to unconnected-(U1-PC6-Pad29).
Connected U1 pin 49 to PWR_NEG.
Connected U1 pin 49 to PWR_NEG.
Add net unconnected-(U1-PC15-OSC32_OUT-Pad4).
Connected U1 pin 4 to unconnected-(U1-PC15-OSC32_OUT-Pad4).
Add net unconnected-(U1-PB14-Pad27).
Connected U1 pin 27 to unconnected-(U1-PB14-Pad27).
Connected U1 pin 49 to PWR_NEG.
Connected U1 pin 49 to PWR_NEG.
Add net unconnected-(U1-PA3-Pad11).
Connected U1 pin 11 to unconnected-(U1-PA3-Pad11).
Connected U1 pin 49 to PWR_NEG.
Connected U1 pin 41 to BTN_DN_N.
Add net unconnected-(U1-PC11-Pad40).
Connected U1 pin 40 to unconnected-(U1-PC11-Pad40).
Connected U1 pin 12 to V_in_ADC.
Connected U1 pin 2 to U6_FLT.
Add net SENSE_TEMP_PWR.
Connected U1 pin 14 to SENSE_TEMP_PWR.
Add net unconnected-(U1-PA2-Pad10).
Connected U1 pin 10 to unconnected-(U1-PA2-Pad10).
Add net unconnected-(U1-PB12-Pad25).
Connected U1 pin 25 to unconnected-(U1-PB12-Pad25).
Connected U1 pin 45 to I2C CLK.
Connected U1 pin 3 to BTN_RT_N.
Connected U1 pin 23 to CTRL_3V3.
Connected U1 pin 49 to PWR_NEG.
Connected U1 pin 49 to PWR_NEG.
Connected U1 pin 49 to PWR_NEG.
Connected U1 pin 19 to Net-(D8-DIN).
Add net unconnected-(U1-PB5-Pad43).
Connected U1 pin 43 to unconnected-(U1-PB5-Pad43).
Add net unconnected-(U1-PB11-Pad24).
Connected U1 pin 24 to unconnected-(U1-PB11-Pad24).
Connected U1 pin 1 to CTRL_3V3.
Connected U1 pin 49 to PWR_NEG.
Connected U1 pin 49 to PWR_NEG.
Connected U1 pin 35 to CTRL_3V3.
Connected U1 pin 7 to Net-(S1-A).
Connected U1 pin 49 to PWR_NEG.
Add net TXD.
Connected U1 pin 32 to TXD.
Add net unconnected-(U1-PB15-Pad28).
Connected U1 pin 28 to unconnected-(U1-PB15-Pad28).
Connected U1 pin 47 to BTN_ENT_N.
Add net unconnected-(U1-PB8-BOOT0-Pad46).
Connected U1 pin 46 to unconnected-(U1-PB8-BOOT0-Pad46).
Connected U1 pin 13 to V_in_ON.
Connected U1 pin 5 to Net-(U1-PF0-OSC_IN).
Connected U1 pin 36 to SWDIO.
Connected U1 pin 49 to PWR_NEG.
Connected U1 pin 20 to CTRL_3V3.
Connected U1 pin 49 to PWR_NEG.
Add net unconnected-(U1-PA1-Pad9).
Connected U1 pin 9 to unconnected-(U1-PA1-Pad9).
Connected U1 pin 21 to CTRL_3V3.
Add net V_out.
Added U2 (footprint 'Package_SON:Infineon_PG-TDSON-8_6.15x5.15mm').
Changed REF** reference designator to U2.
Changed U2 value from Infineon_PG-TDSON-8_6.15x5.15mm to BSC112N06LD.
Updated U2 symbol association from  to /2e9cd074-cfb4-49be-b732-5128a80bbf81.
Updated U2 fields.
Updated U2 sheetname to '/'.
Updated U2 sheetfile to 'Solar Project.kicad_sch'.
Connected U2 pin 5 to /PV_IN_POS_FUSED.
Connected U2 pin 5 to /PV_IN_POS_FUSED.
Connected U2 pin 5 to /PV_IN_POS_FUSED.
Connected U2 pin 5 to /PV_IN_POS_FUSED.
Connected U2 pin 4 to Net-(U2-G1).
Connected U2 pin 5 to /PV_IN_POS_FUSED.
Connected U2 pin 2 to Net-(U2-G1).
Connected U2 pin 3 to Net-(U2-S1).
Connected U2 pin 1 to Net-(U2-S1).
Connected C3 pin 1 to V_out.
Added U3 (footprint 'PCM_JLCPCB:WQFN-28_L5.0-W5.0-P0.50-BL-EP3.2').
Changed REF** reference designator to U3.
Changed U3 value from WQFN-28_L5.0-W5.0-P0.50-BL-EP3.2 to CP2102-GMR.
Updated U3 symbol association from  to /93341972-d285-4090-bebc-4febfb7c0cc4.
Updated U3 fields.
Updated U3 sheetname to '/'.
Updated U3 sheetfile to 'Solar Project.kicad_sch'.
Add net unconnected-(U3-NC-Pad17).
Connected U3 pin 17 to unconnected-(U3-NC-Pad17).
Connected U3 pin 26 to TXD.
Add net unconnected-(U3-NC-Pad10).
Connected U3 pin 10 to unconnected-(U3-NC-Pad10).
Connected U3 pin 9 to Net-(U3-RST#).
Connected U3 pin 3 to PWR_NEG.
Add net unconnected-(U3-SUSPEND-Pad12).
Connected U3 pin 12 to unconnected-(U3-SUSPEND-Pad12).
Updated R61 fields.
Connected U3 pin 21 to unconnected-(U3-NC-Pad21).
Add net unconnected-(U3-NC-Pad22).
Connected U3 pin 22 to unconnected-(U3-NC-Pad22).
Add net unconnected-(U3-EP-Pad29).
Connected U3 pin 29 to unconnected-(U3-EP-Pad29).
Add net unconnected-(U3-NC-Pad15).
Connected U3 pin 15 to unconnected-(U3-NC-Pad15).
Add net unconnected-(U3-EP-Pad29)_1.
Connected U3 pin 29 to unconnected-(U3-EP-Pad29)_1.
Add net unconnected-(U3-EP-Pad29)_2.
Connected U3 pin 29 to unconnected-(U3-EP-Pad29)_2.
Add net unconnected-(U3-EP-Pad29)_3.
Connected U3 pin 29 to unconnected-(U3-EP-Pad29)_3.
Connected U3 pin 8 to VBUS.
Connected U3 pin 23 to CTS.
Add net unconnected-(U3-RI-Pad2).
Connected U3 pin 2 to unconnected-(U3-RI-Pad2).
Add net unconnected-(U3-EP-Pad29)_4.
Connected U3 pin 29 to unconnected-(U3-EP-Pad29)_4.
Add net unconnected-(U3-NC-Pad20).
Connected U3 pin 20 to unconnected-(U3-NC-Pad20).
Add net unconnected-(U3-EP-Pad29)_5.
Connected U3 pin 29 to unconnected-(U3-EP-Pad29)_5.
Add net unconnected-(U3-SUSPEND#-Pad11).
Connected U3 pin 11 to unconnected-(U3-SUSPEND#-Pad11).
Add net unconnected-(U3-EP-Pad29)_6.
Connected U3 pin 29 to unconnected-(U3-EP-Pad29)_6.
Connected U3 pin 7 to VBUS.
Connected U3 pin 4 to Net-(U3-D+).
Add net unconnected-(U3-NC-Pad13).
Connected U3 pin 13 to unconnected-(U3-NC-Pad13).
Connected U3 pin 24 to RTS.
Add net unconnected-(U3-DSR-Pad27).
Connected U3 pin 27 to unconnected-(U3-DSR-Pad27).
Add net unconnected-(U3-NC-Pad18).
Connected U3 pin 18 to unconnected-(U3-NC-Pad18).
Add net unconnected-(U3-EP-Pad29)_7.
Connected U3 pin 29 to unconnected-(U3-EP-Pad29)_7.
Add net unconnected-(U3-NC-Pad14).
Connected U3 pin 14 to unconnected-(U3-NC-Pad14).
Add net unconnected-(U3-EP-Pad29)_8.
Connected U3 pin 29 to unconnected-(U3-EP-Pad29)_8.
Connected U3 pin 5 to Net-(U3-D-).
Add net unconnected-(U3-NC-Pad19).
Connected U3 pin 19 to unconnected-(U3-NC-Pad19).
Add net unconnected-(U3-NC-Pad16).
Connected U3 pin 16 to unconnected-(U3-NC-Pad16).
Connected U3 pin 25 to RXD.
Add net unconnected-(U3-EP-Pad29)_9.
Connected U3 pin 29 to unconnected-(U3-EP-Pad29)_9.
Connected U3 pin 6 to CTRL_3V3.
Add net unconnected-(U3-DTR-Pad28).
Connected U3 pin 28 to unconnected-(U3-DTR-Pad28).
Add net unconnected-(U3-DCD-Pad1).
Connected U3 pin 1 to unconnected-(U3-DCD-Pad1).
Added C4 (footprint 'Capacitor_THT:CP_Radial_D6.3mm_P2.50mm').
Added U4 (footprint 'PCM_JLCPCB:ESOP-8_L4.9-W3.9-P1.27-LS6.0-BL-EP').
Changed REF** reference designator to U4.
Changed U4 value from ESOP-8_L4.9-W3.9-P1.27-LS6.0-BL-EP to LM5163DDAR.
Updated U4 symbol association from  to /588fa2bb-b368-44a6-bb08-e01124692851.
Updated U4 fields.
Updated U4 sheetname to '/'.
Updated U4 sheetfile to 'Solar Project.kicad_sch'.
Updated U4 footprint filters to 'HSOP*1EP*3.9x4.9*P1.27mm*'.
Connected U4 pin 7 to Net-(U4-BST).
Connected U4 pin 1 to PWR_NEG.
Connected U4 pin 8 to Net-(U4-SW).
Connected U4 pin 5 to Net-(U4-FB).
Connected U4 pin 2 to Net-(U4-VIN).
Connected U4 pin 4 to Net-(U4-RON).
Add net unconnected-(U4-PGOOD-Pad6).
Connected U4 pin 6 to unconnected-(U4-PGOOD-Pad6).
Connected U4 pin 3 to Net-(U4-EN/UVLO).
Changed REF** reference designator to C4.
Added U5 (footprint 'Package_SON:Infineon_PG-TDSON-8_6.15x5.15mm').
Changed REF** reference designator to U5.
Changed U5 value from Infineon_PG-TDSON-8_6.15x5.15mm to BSC155N06ND.
Updated U5 symbol association from  to /0ab5d6cb-27de-410f-8e3e-2ba07e6d392d.
Updated U5 fields.
Updated U5 sheetname to '/'.
Updated U5 sheetfile to 'Solar Project.kicad_sch'.
Connected U5 pin 1 to Net-(U5-S1).
Connected U5 pin 3 to Net-(U5-S1).
Connected U5 pin 4 to Net-(U5-G1).
Connected U5 pin 5 to Net-(R16-Pad1).
Connected U5 pin 5 to Net-(R16-Pad1).
Connected U5 pin 5 to Net-(R16-Pad1).
Connected U5 pin 5 to Net-(R16-Pad1).
Connected U5 pin 2 to Net-(U5-G1).
Connected U5 pin 5 to Net-(R16-Pad1).
Changed C4 value from CP_Radial_D6.3mm_P2.50mm to 47uf.
Added U6 (footprint 'Package_DFN_QFN:Texas_RHA0040B_VQFN-40-1EP_6x6mm_P0.5mm_EP4.15x4.15mm').
Changed REF** reference designator to U6.
Changed U6 value from Texas_RHA0040B_VQFN-40-1EP_6x6mm_P0.5mm_EP4.15x4.15mm to LM51772QRHARQ1.
Updated U6 symbol association from  to /d02911ed-2fdd-4ab3-9863-9bbf41ac059b.
Updated U6 fields.
Updated U6 sheetname to '/'.
Updated U6 sheetfile to 'Solar Project.kicad_sch'.
Updated U6 footprint filters to 'RHA0040P-IPC_A RHA0040P-IPC_B RHA0040P-IPC_C RHA0040P-MFG'.
Connected U6 pin 6 to I2C CLK.
Connected U6 pin 11 to U6_FLT.
Connected U6 pin 25 to Net-(U6-HB1).
Connected U6 pin 37 to _Undervoltage Feedback.
Connected U6 pin 22 to Net-(U6-CSA).
Connected U6 pin 4 to PWR_NEG.
Connected U6 pin 14 to _OUTPUT Feedback.
Add net LO1.
Connected U6 pin 27 to LO1.
Connected U6 pin 33 to SW_2.
Add net HO1.
Connected U6 pin 24 to HO1.
Add net ISNSP.
Connected U6 pin 20 to ISNSP.
Connected U6 pin 8 to Net-(U6-CFG2).
Connected U6 pin 7 to Net-(U6-ILIMCOMP_ISET).
Connected U6 pin 21 to Net-(U6-CSB).
Connected U6 pin 17 to PWR_NEG.
Connected U6 pin 3 to PWR_NEG.
Connected U6 pin 29 to U6_VCC2.
Add net unconnected-(U6-DRV1-Pad35).
Connected U6 pin 35 to unconnected-(U6-DRV1-Pad35).
Connected U6 pin 15 to V_in_FB.
Connected U6 pin 5 to I2C DATA.
Add net unconnected-(U6-NC-Pad39).
Connected U6 pin 39 to unconnected-(U6-NC-Pad39).
Connected U6 pin 19 to ISNSN.
Add net HO2.
Connected U6 pin 32 to HO2.
Connected U6 pin 36 to PV_IN_POS.
Connected U6 pin 2 to Net-(U6-SS_ATRK).
Connected U6 pin 40 to PV_IN_POS.
Add net LO2.
Connected U6 pin 30 to LO2.
Connected U6 pin 13 to Net-(U6-COMP).
Connected U6 pin 38 to CTRL_3V3.
Connected U6 pin 9 to Net-(U6-ADDR_SLOPE_CFG1).
Connected U6 pin 12 to Net-(U6-RT).
Connected U6 pin 16 to Net-(U6-ILIMCOMP_ISET).
Connected U6 pin 28 to PGND.
Connected U6 pin 10 to Net-(U6-CDC).
Connected U6 pin 31 to Net-(U6-HB2).
Add net unconnected-(U6-NC-Pad34).
Connected U6 pin 34 to unconnected-(U6-NC-Pad34).
Add net unconnected-(U6-NC-Pad26).
Connected U6 pin 26 to unconnected-(U6-NC-Pad26).
Connected U6 pin 1 to Net-(U6-VCC1).
Connected U6 pin 18 to CHG_OUT_POS.
Connected U6 pin 41 to PWR_NEG.
Connected U6 pin 23 to SW_1.
Updated C4 symbol association from  to /add1db8c-a206-479b-9469-e1b384f65bb2.
Added U7 (footprint '1My_Parts_ ICs:Humidity sensor').
Changed REF** reference designator to U7.
Changed U7 value from Humidity sensor to AHT20.
Updated U7 symbol association from  to /f162de84-6708-4694-bbe5-94439c54019d.
Updated U7 fields.
Updated U7 sheetname to '/'.
Updated U7 sheetfile to 'Solar Project.kicad_sch'.
Add net Net-(U7-NC-Pad1).
Connected U7 pin 6 to Net-(U7-NC-Pad1).
Connected U7 pin 3 to I2C CLK.
Connected U7 pin 1 to Net-(U7-NC-Pad1).
Connected U7 pin 2 to CTRL_3V3.
Connected U7 pin 4 to I2C DATA.
Connected U7 pin 5 to PWR_NEG.
Updated C4 fields.
Added U8 (footprint '1My_Parts_ ICs:0.96 inOLED display SSD1306').
Changed U1 reference designator to U8.
Updated U8 symbol association from  to /633f5c57-7250-4230-a874-af4e614e0b01.
Updated U8 sheetname to '/'.
Updated U8 sheetfile to 'Solar Project.kicad_sch'.
Updated U8 footprint filters to 'EA?T123X?I2C*'.
Connected U8 pin 2 to CTRL_3V3.
Connected U8 pin 6 to PWR_NEG.
Connected U8 pin 8 to PWR_NEG.
Connected U8 pin 4 to I2C DATA.
Connected U8 pin 5 to PWR_NEG.
Connected U8 pin 3 to I2C CLK.
Connected U8 pin 7 to PWR_NEG.
Connected U8 pin 1 to PWR_NEG.
Updated C4 sheetname to '/'.
Added U9 (footprint 'Package_SO:SOIC-8-1EP_3.9x4.9mm_P1.27mm_EP2.29x3mm_ThermalVias').
Changed REF** reference designator to U9.
Changed U9 value from SOIC-8-1EP_3.9x4.9mm_P1.27mm_EP2.29x3mm_ThermalVias to LMV393.
Updated U9 symbol association from  to /fd68691f-26c8-4428-bf98-d2d020dc6c58.
Updated U9 fields.
Updated U9 sheetname to '/'.
Updated U9 sheetfile to 'Solar Project.kicad_sch'.
Updated U9 footprint filters to 'SOIC*3.9x4.9mm*P1.27mm* TSSOP*4.4x3mm*P0.65mm* VSSOP*3x3mm*P0.65mm* VSSOP*2.3x2mm*P0.5mm*'.
Connected U9 pin 5 to OCP_SENSE.
Connected U9 pin 2 to OVP_REF.
Connected U9 pin 4 to PWR_NEG.
Connected U9 pin 7 to FAULT_OCP.
Connected U9 pin 8 to CTRL_3V3.
Connected U9 pin 3 to OVP_SENSE.
Connected U9 pin 6 to OCP_REF.
Connected U9 pin 1 to FAULT_OVP.
Updated C4 sheetfile to 'Solar Project.kicad_sch'.
Added U10 (footprint 'PCM_JLCPCB:SOT-363_SC-70-6').
Changed REF** reference designator to U10.
Changed U10 value from SOT-363_SC-70-6 to INA213AIDCKR.
Updated U10 symbol association from  to /14e08295-8c93-46a8-8451-c6d99eca8fda.
Updated U10 fields.
Updated U10 sheetname to '/'.
Updated U10 sheetfile to 'Solar Project.kicad_sch'.
Connected U10 pin 1 to PWR_NEG.
Connected U10 pin 4 to ISNSP.
Connected U10 pin 5 to ISNSN.
Connected U10 pin 2 to PWR_NEG.
Connected U10 pin 3 to CTRL_3V3.
Connected U10 pin 6 to OCP_MEAS.
Updated C4 footprint filters to 'C_*'.
Added X2 (footprint 'PCM_JLCPCB:CRYSTAL-SMD_L11.5-W4.8-LS12.7').
Changed REF** reference designator to X2.
Changed X2 value from CRYSTAL-SMD_L11.5-W4.8-LS12.7 to X49SM8MSD2SC.
Updated X2 symbol association from  to /ea5c80b6-c8f3-4b31-a157-91c5e3170614.
Updated X2 fields.
Updated X2 sheetname to '/'.
Updated X2 sheetfile to 'Solar Project.kicad_sch'.
Connected X2 pin 1 to Net-(U1-PF0-OSC_IN).
Connected X2 pin 2 to Net-(U1-PF1-OSC_OUT).

Add net unconnected-(U3-NC-Pad21).
Warning: No net found for component M2 pad 2 (no pin 2 in symbol).
Warning: No net found for component U9 pad 9 (no pin 9 in symbol).
Warning: No net found for component U9 pad 9 (no pin 9 in symbol).
Warning: No net found for component M1 pad 5 (no pin 5 in symbol).
Warning: No net found for component J5 pad A1 (no pin A1 in symbol).
Warning: No net found for component J5 pad B4 (no pin B4 in symbol).
Warning: No net found for component M2 pad 3 (no pin 3 in symbol).
Warning: No net found for component M1 pad 3 (no pin 3 in symbol).
Warning: No net found for component M2 pad 1 (no pin 1 in symbol).
Warning: No net found for component M4 pad 1 (no pin 1 in symbol).
Warning: No net found for component U9 pad 9 (no pin 9 in symbol).
Warning: No net found for component U9 pad 9 (no pin 9 in symbol).
Warning: No net found for component U9 pad 9 (no pin 9 in symbol).
Warning: No net found for component U9 pad 9 (no pin 9 in symbol).
Warning: No net found for component U9 pad 9 (no pin 9 in symbol).
Warning: No net found for component U9 pad 9 (no pin 9 in symbol).
Warning: No net found for component M4 pad 4 (no pin 4 in symbol).
Warning: No net found for component M3 pad 3 (no pin 3 in symbol).
Warning: No net found for component J5 pad B1 (no pin B1 in symbol).
Warning: No net found for component M1 pad 2 (no pin 2 in symbol).
Warning: No net found for component M1 pad 1 (no pin 1 in symbol).
Warning: No net found for component M4 pad 5 (no pin 5 in symbol).
Warning: No net found for component U4 pad 9 (no pin 9 in symbol).
Warning: No net found for component U4 pad 9 (no pin 9 in symbol).
Warning: No net found for component J5 pad B12 (no pin B12 in symbol).
Warning: No net found for component U4 pad 9 (no pin 9 in symbol).
Warning: No net found for component M4 pad 2 (no pin 2 in symbol).
Warning: No net found for component J5 pad A4 (no pin A4 in symbol).
Warning: No net found for component U4 pad 9 (no pin 9 in symbol).
Warning: No net found for component J5 pad B9 (no pin B9 in symbol).
Warning: No net found for component U4 pad 9 (no pin 9 in symbol).
Warning: No net found for component M3 pad 2 (no pin 2 in symbol).
Warning: No net found for component M3 pad 1 (no pin 1 in symbol).
Warning: No net found for component U4 pad 9 (no pin 9 in symbol).
Warning: No net found for component M2 pad 5 (no pin 5 in symbol).
Warning: No net found for component J5 pad A12 (no pin A12 in symbol).
Warning: No net found for component M3 pad 5 (no pin 5 in symbol).
Warning: No net found for component U4 pad 9 (no pin 9 in symbol).
Warning: No net found for component M1 pad 4 (no pin 4 in symbol).
Warning: No net found for component M3 pad 4 (no pin 4 in symbol).
Warning: No net found for component M2 pad 4 (no pin 4 in symbol).
Warning: No net found for component M4 pad 3 (no pin 3 in symbol).
Warning: No net found for component J5 pad A9 (no pin A9 in symbol).
Error: J5 pad A9B4 not found in Connector_USB:USB_C_Receptacle_G-Switch_GT-USB-7010ASV.
Error: J5 pad B9A4 not found in Connector_USB:USB_C_Receptacle_G-Switch_GT-USB-7010ASV.
Error: M1 pad G not found in Package_TO_SOT_SMD:TDSON-8-1.
Error: M1 pad D not found in Package_TO_SOT_SMD:TDSON-8-1.
Error: M1 pad S not found in Package_TO_SOT_SMD:TDSON-8-1.
Error: M2 pad G not found in Package_TO_SOT_SMD:TDSON-8-1.
Error: M2 pad S not found in Package_TO_SOT_SMD:TDSON-8-1.
Error: M2 pad D not found in Package_TO_SOT_SMD:TDSON-8-1.
Error: M3 pad G not found in Package_TO_SOT_SMD:TDSON-8-1.
Error: M3 pad S not found in Package_TO_SOT_SMD:TDSON-8-1.
Error: M3 pad D not found in Package_TO_SOT_SMD:TDSON-8-1.
Error: M4 pad G not found in Package_TO_SOT_SMD:TDSON-8-1.
Error: M4 pad S not found in Package_TO_SOT_SMD:TDSON-8-1.
Error: M4 pad D not found in Package_TO_SOT_SMD:TDSON-8-1.
Error: R16 pad 3 not found in Resistor_SMD:R_2512_6332Metric.
Error: R16 pad 4 not found in Resistor_SMD:R_2512_6332Metric.
Error: R22 pad 4 not found in Resistor_SMD:R_2512_6332Metric.
Error: R22 pad 3 not found in Resistor_SMD:R_2512_6332Metric.
Error: U2 pad 6 not found in Package_SON:Infineon_PG-TDSON-8_6.15x5.15mm.
Error: U2 pad 7 not found in Package_SON:Infineon_PG-TDSON-8_6.15x5.15mm.
Error: U2 pad 8 not found in Package_SON:Infineon_PG-TDSON-8_6.15x5.15mm.
Error: U5 pad 7 not found in Package_SON:Infineon_PG-TDSON-8_6.15x5.15mm.
Error: U5 pad 8 not found in Package_SON:Infineon_PG-TDSON-8_6.15x5.15mm.
Error: U5 pad 6 not found in Package_SON:Infineon_PG-TDSON-8_6.15x5.15mm.
Error: J5 pad A12B1 not found in Connector_USB:USB_C_Receptacle_G-Switch_GT-USB-7010ASV.
Error: J5 pad B12A1 not found in Connector_USB:USB_C_Receptacle_G-Switch_GT-USB-7010ASV.
Error: Cannot add TH1 (no footprint assigned).

Info: Total warnings: 43, errors: 27.
