Phil-CIA/Solar-Project-200w/NEW_CHAT_HANDOFF_SHORT.rmd

# Solar Project Quick Handoff (2026-08-08)

Session checkpoint:
- Rev 1 now includes a 5 V-powered ESP32-C3 development module for Wi-Fi.
- DEC-015 locks the ESP32 as a network coprocessor; STM32 retains all charger and safety authority.
- UART TX/RX is the baseline processor link, with RTS/CTS optional.

Architecture baseline:
- ESP32 `5V` pin uses `CTRL_5V`; exposed `3.3V` pin remains unused.
- U5 independently generates `CTRL_3V3`.
- Use versioned COBS frames with sequence, length, and CRC16.
- ESP32 owns provisioning, MQTT/HTTPS, and ESP32 OTA only.

Open verification:
- Regenerate ERC; the checked-in clean report is dated 2026-08-04.
- Verify D10 direction, USB/`CTRL_5V` budget, antenna keepout, UART mapping, and reset/boot needs.
- C52 voltage-rating margin remains open.

First move next session:
1. Read HANDOFF.md, SOLAR_HANDOFF_2026-08-08.md, and docs/wifi-coprocessor-architecture.md.
2. Export fresh ERC from the Rev 1 schematic.
3. Close the ESP32 hardware-interface verification items, then define the initial UART and MQTT schemas.

Paste prompt:
Continue in Solar-Project-200w from SOLAR_HANDOFF_2026-08-08.md. Preserve DEC-015: STM32 owns charger safety and the 5 V-powered ESP32-C3 development module is a network coprocessor. Regenerate ERC, verify D10 and the CTRL_5V current budget, confirm UART/RTS/CTS/reset pin mapping and antenna keepout, then define the initial framed-UART and MQTT telemetry schemas.
