Phil-CIA/Solar-Project-200w/SOLAR_HANDOFF_2026-07-20.md

# Solar Project Handoff - 2026-07-20 Recovery Stop

Status: Session went off-track during mixed schematic/erc cleanup attempts. Documentation cleanup progressed, but schematic-level closure is not yet complete. Treat this handoff as the authoritative restart point.

Date: 2026-07-20
Phase: Phase 1 - Rev 0 schematic cleanup
Outcome: Planning and ownership rules are clearer; schematic closure and clean ERC are still open.

---

## 1) What Is Solid Right Now

1. Cleanup ownership rules are documented and aligned across planning files.
2. Sheet 2 docs now state that CTRL_PWM_MAIN is the active Rev 0 control-drive path.
3. Control/fault defaults are explicit:
   - keep CTRL_EN_CHG
   - keep FAULT_OCP
   - keep FAULT_OVP
   - V_in_ON defaults to delete unless legacy branch is intentionally retained
4. U6 helper-net defaults are explicit:
   - U6_VCC2 should be closed with decoupling
   - U6_FLT should be closed with pull-up
   - U6 strap nets remain keep-only-if-intentional

---

## 2) What Is Not Closed

1. Fresh ERC still reports active errors and warnings from the current on-disk state.
2. Schematic closure is not complete enough to call the migration cleanup done.
3. The session introduced high churn while trying to combine schematic edits and ERC closure in one pass.

---

## 3) Current Working-Tree Snapshot

Modified files at stop include:

1. HANDOFF.md
2. SOLAR_PROJECT_CONCEPT_AND_HANDOFF.md
3. docs/decisions-log.md
4. docs/session-plan-2026-07-20.md
5. hardware/mppt/buck-power-stage-wiring-map.md
6. hardware/mppt/kicad-implementation-checklist.md
7. hardware/mppt/schematic-notes.md
8. hardware/mppt/sheet2-component-picks.md
9. hardware/kicad/solar-project/Solar Project.kicad_sch
10. hardware/kicad/solar-project/fp-info-cache

---

## 4) Recovery Rules For Next Session

1. Treat on-disk schematic as source of truth for this restart.
2. Do not batch many schematic edits before re-running ERC.
3. Make one focused class of fix at a time:
   - power-authority
   - symbol-pin typing
   - legacy net retirement
4. After each focused class, re-run ERC and log delta in notes.
5. Keep docs and schematic commits separate.

---

## 5) Safe Restart Sequence

1. Run git status --short and confirm file state.
2. Open hardware/kicad/solar-project/Solar Project.kicad_sch and visually verify U6, R34, and local helper rails before edits.
3. Re-run ERC from KiCad GUI and export fresh ERC.rpt and Solar Project.net.
4. Use that fresh report as baseline and fix only one error class first.
5. Update hardware/mppt/schematic-notes.md with evidence after each pass.

---

## 6) First Focus When Resuming

Start with ERC hard errors only (not warnings), then stop and reassess before touching warning cleanup.

If the hard errors drop cleanly, proceed to net-retirement decisions (V_in_ON and legacy U2/Q2 branch) with explicit ownership notes.

---

## 7) Exit Criteria For The Next Session

1. New ERC baseline captured with timestamp.
2. At least one hard-error class resolved and documented.
3. No ambiguous ownership language left for CTRL_EN_CHG, FAULT_OCP, FAULT_OVP, and V_in_ON.
4. Next action captured in HANDOFF.md.

---

## 8) Session Closeout Addendum (Same Date)

1. The parser-corrupted schematic attempts were not used as the final source.
2. `hardware/kicad/solar-project/Solar Project.kicad_sch` was restored from:
   - `hardware/kicad/solar-project/Solar Project-backups/Solar Project-2026-07-20_050545.zip`
3. KiCad-path sync to GitHub was completed in commit:
   - `b8839b9` (`kicad: sync schematic and cache from local recovery`)
4. This handoff remains the authoritative restart logic for ERC-first recovery sequencing.
