Phil-CIA/Solar-Project-200w/SOLAR_HANDOFF_2026-07-13.md

# Solar Project 200W - Handoff (2026-07-13)

## Session Summary

**Date**: 2026-07-13  
**Phase**: Phase 1 implementation refinement (Rev 0)  
**Focus**: close stale session state, preserve local progress, and hand off a clean restart plan

---

## What Is Already Pushed To Remote

- Commit `728ef1a` is on `main` and `origin/main`.
- DEC-005 is closed for Rev 0 with STM32G431 baseline in `docs/decisions-log.md`.
- STM32G431 first-pass pin budget is documented in `docs/session-plan-2026-07-10.md`.
- Zone D STM32 mapping is documented in `hardware/mppt/sheet4-sensing-control-wiring-map.md`.

---

## Local (Uncommitted) State At Stop

From `git status --short` at stop:

- Modified: `docs/session-plan-2026-07-10.md`
- Modified: `hardware/kicad/solar-project/Solar Project.kicad_sch`
- Modified: `hardware/mppt/kicad-implementation-checklist.md`
- Modified: `hardware/mppt/schematic-notes.md`
- Untracked: `hardware/mppt/pre-routing-blockers-2026-07-10.md`
- Untracked: `hardware/mppt/rev0-component-shortlist-2026-07-10.md`
- Untracked: `hardware/kicad/solar-project/_autosave-Solar Project.kicad_sch`

Important:
- The working tree includes both documentation changes and schematic edits.
- Do not mix autosave artifacts into intentional commits.

---

## Technical State Snapshot

### Decisions and Scope

- Rev 0 remains asynchronous buck baseline (DEC-003).
- Rev 0 controller baseline is STM32G431 (DEC-005).
- Rev 1 remains the place for synchronous/gate-driver and ideal-diode upgrades.

### Validation and Planning Artifacts Created Locally

- Requirements validation sweep notes are added in `hardware/mppt/schematic-notes.md`.
- Rev 0 shortlist with margin/risk fields is in `hardware/mppt/rev0-component-shortlist-2026-07-10.md`.
- Pre-routing blocker queue is in `hardware/mppt/pre-routing-blockers-2026-07-10.md`.

### Current Pre-Routing Gate Status

Status: **BLOCKED**

Must-fix items captured in blocker file:
1. `SENSE_PV_I` collision with `CHG_OUT_POS`.
2. `SENSE_BAT_I` collision with `BAT_BUS_POS`.
3. Dangling fault nets `FAULT_OCP` and `FAULT_OVP` ownership.

---

## Next Session Priority Order

1. Clean local workspace state and separate intentional changes from autosave artifacts.
2. Resolve current-sense net collisions in `Solar Project.kicad_sch`.
3. Resolve fault-net ownership/termination strategy in schematic and notes.
4. Run ERC again and record a fresh snapshot in `hardware/mppt/schematic-notes.md`.
5. Commit in small chunks:
   - docs-only commit
   - schematic/ERC fix commit

---

## Safe First Actions Next Session

1. Run `git status --short` and verify the same local file set is present.
2. Keep `_autosave-Solar Project.kicad_sch` out of commits.
3. Review these files first:
   - `SOLAR_HANDOFF_2026-07-13.md`
   - `hardware/mppt/pre-routing-blockers-2026-07-10.md`
   - `hardware/mppt/rev0-component-shortlist-2026-07-10.md`
   - `hardware/mppt/schematic-notes.md`
4. Continue with blocker fix order from `hardware/mppt/pre-routing-blockers-2026-07-10.md`.

---

## Suggested Commit Plan (When Ready)

1. Docs commit:
   - `docs/session-plan-2026-07-10.md`
   - `hardware/mppt/schematic-notes.md`
   - `hardware/mppt/rev0-component-shortlist-2026-07-10.md`
   - `hardware/mppt/pre-routing-blockers-2026-07-10.md`
2. Schematic commit:
   - `hardware/kicad/solar-project/Solar Project.kicad_sch`
   - optional updated ERC report if regenerated

Leave these out unless explicitly intended:
- `hardware/kicad/solar-project/_autosave-Solar Project.kicad_sch`

---

## Closeout

Session is now safely parked with a dated handoff and explicit restart plan.
