Phil-CIA/Solar-Project-200w/docs/decisions-log.md

# Solar Project 200W - Decisions Log

Last updated: 2026-08-31 (DEC-022 D8 supply isolation)
Decision owners: Phil + Copilot
Decision policy: move fast, log every non-trivial choice, and defer only with a target date.

## How We Use This Log

1. Record each meaningful technical or process choice the same day it is made.
2. If a decision is deferred, assign an owner and target decision date.
3. Link each decision to impacted requirements or architecture sections once those docs are created.
4. Review unresolved items at least once per week or at the start of any design session.

## Status Legend

- Decided: accepted baseline for current phase.
- Deferred: intentionally delayed until prerequisite information exists.
- Open: needs discussion now; blocks near-term progress.

## Decision Register

| ID | Date | Topic | Decision | Status | Rationale | Impact | Owner | Target Date |
|---|---|---|---|---|---|---|---|---|
| DEC-001 | 2026-07-06 | Planning approach | Use agile, short-cycle planning for concept phase with decision-first documentation. | Decided | Team size is two; high communication bandwidth supports rapid iteration. | Faster concept-to-design transition with explicit traceability. | Phil + Copilot | 2026-07-06 |
| DEC-002 | 2026-07-06 | Current phase scope | Complete planning docs before hardware or firmware implementation expansion. | Decided | Reduces rework and safety risk by clarifying constraints first. | Focuses effort on requirements, architecture, and decision clarity. | Phil + Copilot | 2026-07-06 |
| DEC-003 | 2026-07-08 | MPPT topology and revision scope | Lock Rev 0 to asynchronous buck implementation; defer synchronous buck and dedicated gate-driver architecture to Rev 1 planning. | Decided | Keeps current schematic and routing work stable while preserving a clear upgrade path after bring-up data. | Unblocks Rev 0 Sheet 2 completion and routing; creates explicit Rev 1 efficiency backlog. | Phil + Copilot | 2026-07-08 |
| DEC-004 | 2026-07-06 | Panel wiring strategy | Use two Renogy 100W panels in series as the Phase 1 design baseline. | Decided | Series reduces PV-side current, simplifies current handling, and aligns naturally with a buck-oriented charger path into a 4S LiFePO4 battery. | Establishes the working PV input envelope for MPPT design and protection sizing. | Phil + Copilot | 2026-07-06 |
| DEC-005 | 2026-07-10 | Charger control approach | Select STM32G431 as Rev 0 baseline MCU for control/telemetry prototyping. Re-evaluate MCU choice at each revision; no production lock-in at this stage. | Decided | Prototype-first workflow, low unit volume (2 boards/rev), and rapid iteration priority outweigh strict cost optimization. | Unblocks concrete pin mapping, firmware scaffold, and migration from U_CTRL placeholder to MCU-defined interfaces. | Phil + Copilot | 2026-07-10 |
| DEC-006 | 2026-07-06 | Telemetry baseline | Start with local serial logging and reserve wireless integration as future extension. | Decided | Keeps bring-up simple while preserving growth path. | Simplifies early firmware and test infrastructure. | Phil + Copilot | 2026-07-06 |
| DEC-007 | 2026-07-06 | Safety-first gating | Require protection strategy coverage before design expansion (fusing, UVLO/OVP/OCP/OTP, reverse polarity, transient protection). | Decided | Safety constraints should be first-class requirements, not afterthoughts. | Guides requirements and architecture definitions immediately. | Phil + Copilot | 2026-07-06 |
| DEC-008 | 2026-07-06 | Validation style | Use staged bench bring-up with current-limited progression and logged checkpoints. | Decided | Reduces risk during early integration and debugging. | Affects future test plan and bring-up checklist structure. | Phil + Copilot | 2026-07-06 |
| DEC-009 | 2026-07-06 | Phase 0 exit | Declare Phase 0 complete once requirements, architecture, decisions, traceability, bring-up checklist, and validation plan are present. | Decided | Establishes a clear phase gate and prevents planning churn. | Enables transition to Phase 1 implementation exploration. | Phil + Copilot | 2026-07-06 |
| DEC-010 | 2026-07-06 | Phase 1 execution mode | Use rapid decision closure with conservative fallback assumptions when blocker data is unavailable in-session. | Decided | Maintains momentum while preserving safety boundaries and traceability. | Prevents schedule stall during early implementation exploration. | Phil + Copilot | 2026-07-06 |
| DEC-011 | 2026-07-06 | Temporary MPPT bounds | Apply temporary planning bounds: 15A continuous charge path assumption and dual panel-wiring envelope modeling until Q-001 and DEC-004 are closed. | Decided | Enables immediate schematic exploration while waiting for final battery and wiring constraints. | Allows Phase 1 design activity without unsafe implicit assumptions. | Phil + Copilot | 2026-07-06 |
| DEC-012 | 2026-07-08 | PV reverse-path optimization | Keep series Schottky reverse-polarity path for Rev 0; evaluate ideal-diode MOSFET replacement in Rev 1. | Deferred | Rev 0 prioritizes simple bring-up and lower integration risk. | Ideal-diode footprint and topology changes move to Rev 1 efficiency optimization work. | Phil + Copilot | 2026-07-20 |
| DEC-013 | 2026-07-14 | STM32G431 control-rail architecture (Rev 0) | Use a single wide-input buck as the primary control rail generator for `CTRL_3V3`, with PV-first runtime sourcing and protected USB bench fallback when PV is absent. Keep battery-domain assist optional through protected source OR-ing into the control-supply input boundary. | Decided | Satisfies required PV-only startup and USB-only bench bring-up without forcing a full dual-converter redesign. Keeps Rev 0 integration complexity bounded while preserving source-flexibility for bring-up and debug. | Unblocks explicit power-tree implementation for MCU VDD/VDDA, clarifies source-priority behavior, and enables targeted startup/noise verification before pre-routing gate closure. | Phil + Copilot | 2026-07-14 |
| DEC-014 | 2026-07-26 | Rev 0 MCU continuity swap | Select `STM32F411CEU6` as the Rev 0 MCU replacement for in-stock continuity, with `STM32F401CEU6` as the immediate backup and `STM32G431CBT6` as the family-continuity fallback. 2026-08-26: this migration was never actually implemented in the schematic. Only the `Value`/`MP` text fields were edited; the symbol `lib_id` remained `1My_MPUs:STM32G431CBU6`, so the board was routed with G431 pin assignments. See DEC-018. | Decided (implementation defective) | The original `STM32G431CBU6` is out of stock, but the reduced Rev 0 control scope still fits the F4 family well enough to keep the current UFQFPN-48 footprint and avoid a package reroute. The assumption that the shared UFQFPN-48 package implied a compatible pinout was incorrect. | Preserves build continuity and limits board-level churn while accepting a firmware migration from G4 to F4. As implemented, it produced an unusable Rev 0 board with hard supply shorts. | Phil + Copilot | 2026-07-26 |
| DEC-015 | 2026-08-08 | Rev 1 Wi-Fi architecture | Use a 5 V-powered ESP32-C3 development module as a network coprocessor. Keep all charging and safety authority in the STM32; connect the processors through a versioned, CRC-protected framed UART protocol. | Decided | Separating network services from real-time charger control prevents Wi-Fi or ESP32 failures from affecting safe operation while retaining provisioning, telemetry, and remote-access capability. | Adds `CTRL_5V` ESP32 power, UART TX/RX with optional RTS/CTS, ESP32-owned Wi-Fi/NVS/MQTT/OTA, and an explicit remote-command validation boundary at the STM32. | Phil + Copilot | 2026-08-08 |
| DEC-016 | 2026-08-26 | Rev 1 QFN exposed-pad footprint correction | Add a via array in the exposed thermal pad of fine-pitch QFN parts (starting with the STM32 footprint) for reflow solder relief, and widen the solder-mask dam between the exposed pad and perimeter pads at all four corners, with particular margin at the pad 1/48 (`CTRL_3V3`) corner and the pad 24/25 (`PWR_NEG`) corner. | Decided | Rev 0 bench bring-up found a persistent 0.7 ohm `CTRL_3V3`-to-`PWR_NEG` short at U1 that survived repeated clean rework; the pad 24/49 corner (same net, tight clearance) is suspected as a channel for solder to migrate under the package toward the pad 1/48 corner during reflow. | Establishes a general exposed-pad footprint rule for future fine-pitch QFN placements, not just U1, to reduce hand-assembly bridging risk. | Phil + Copilot | 2026-08-26 |
| DEC-017 | 2026-08-26 | Rev 0 U1 short root cause (superseded by DEC-018) | Superseded 2026-08-26. Originally concluded the short was a footprint/exposed-pad clearance defect. The actual root cause is a symbol/part pinout mismatch documented in DEC-018. | Superseded | Cross-testing correctly ruled out a single bad chip and a single bad board, but the shared cause was the schematic symbol, not the footprint geometry. | Retained for traceability of the debugging path. | Phil + Copilot | 2026-08-26 |
| DEC-018 | 2026-08-26 | Rev 0 U1 short confirmed root cause | The Rev 0 board was routed against the `1My_MPUs:STM32G431CBU6` symbol while `STM32F411CEU6` parts were fitted. Only the `Value` and `MP` text fields were changed during the DEC-014 part migration; the symbol `lib_id` and therefore the pin mapping were never updated. The two devices have incompatible power pin assignments in UFQFPN-48, producing hard supply shorts through the die. | Decided | Verified against the project G431 symbol and KiCad's official `STM32F411CEUx` library: board pads 23 and 35 carry `CTRL_3V3` but are `VSS` on F411, and pad 24 carries `PWR_NEG` but is `VDD` on F411. This creates two independent short paths (`CTRL_3V3` to internal ground metal out through exposed pad 49 to `PWR_NEG`, and `PWR_NEG` to the internal VDD rail out through pad 48 to `CTRL_3V3`). The approximately 0.7 ohm reading is bond-wire and internal metallization resistance, which no rework can correct. | Existing Rev 0 boards are correctly routed for `STM32G431CBU6` and should work if that part is fitted. Fitting `STM32F411CEU6` is not viable on this layout. Rev 1 must update the actual symbol, not just the value field, and re-verify the full pin map before routing. Also invalidates the DEC-016 premise as the cause, though the footprint improvements remain good practice. | Phil + Copilot | 2026-08-26 |
| DEC-019 | 2026-08-26 | Rev 0 I2C SCL/SDA swap | The Rev 0 I2C bus is wired with clock and data reversed at the MCU. `PB6` (pad 44) carries `I2C DATA` to the U7/U8 SDA pins, and `PB7` (pad 45) carries `I2C CLK` to the U7/U8 SCL pins. On STM32G4, `PB6` is `I2C1_SCL` only and `PB7` is `I2C1_SDA` only, with no alternate function that reverses them. Use a software bit-banged I2C driver on these two GPIOs for Rev 0 bring-up; fix the assignment properly in Rev 1. | Decided | The peripheral side is self-consistent (`I2C CLK` lands on SCL and `I2C DATA` lands on SDA at both U7 and U8), so the error is isolated to the MCU pin assignment. Bit-banging avoids cutting traces on boards that already have significant rework history. | Hardware `I2C1` is unusable on Rev 0 as routed. Adds a software I2C driver task to Rev 0 firmware and a net-reassignment task to Rev 1. A two-trace cut-and-jumper rework remains available if hardware I2C is later required. | Phil + Copilot | 2026-08-26 |
| DEC-020 | 2026-08-26 | MCU sourcing and revision strategy | Order two `STM32G473CEU6` (UFQFPN-48) to recover the existing Rev 0 boards, and target a properly implemented `STM32F411` migration for Rev 1. Do not order additional G4 stock beyond the Rev 0 recovery need. | Decided | The Rev 0 layout is already correctly routed for the G4 UFQFPN-48 pin map, so a G4 part is the only way to make existing boards work without a re-spin. Verified `STM32G473CEU6` is pin-identical to the routed `STM32G431CBU6` map across all 49 pins. Longer term, the F411 is more common and easier to source, so Rev 1 should carry that migration properly rather than perpetuating G4. | Limits G4 spend to board recovery only. Rev 1 must replace the actual symbol with KiCad's official `STM32F411CEUx`, re-assign every net, add the `VCAP1` capacitor, connect `VDDA`/`VSSA`, resolve `BOOT0`/`BOOT1`, and re-route the MCU area under the Section 7.2 Part Substitution Gate. | Phil + Copilot | 2026-08-26 |
| DEC-021 | 2026-08-31 | Deterministic MCU BOOT0 bias | Add a populated 10 kOhm resistor from MCU BOOT0 to `PWR_NEG` and an accessible BOOT0 test point in Rev 1. Keep the option-byte selection configured for normal user-flash boot as defense in depth. | Decided | Rev 0 left `PB8/BOOT0` floating and repeatedly entered system memory on physical power-up even though PB8 later measured low. Rev 0 required `nSWBOOT0=0`, `nBOOT0=1` to boot reliably without risky QFN-pad rework. | Rev 1 must have a deterministic hardware boot state and permit direct BOOT0 probing or override during bring-up; the resistor footprint is populated by default, not DNI. | Phil + Copilot | 2026-08-31 |
| DEC-022 | 2026-08-31 | D8 supply isolation from U6 VCC2 | Do not power D8 from LM51772 VCC2. Rev 0 moved D8 pad 2 to USB `VBUS` and uses USB as the sole VBUS source during D8 testing. Rev 1 shall route D8 to a qualified 5 V rail, add local 100 nF bypass, and include a deliberate supply isolation link or resistor footprint. | Decided; Rev 0 rework accepted with documented residual risk | TI LM51772-Q1 Rev. A Section 7.3.7.2 explicitly prohibits external loads on VCC2. The fitted XL-1615RGBC-WS2812B specifies a 3.5-5.5 V application supply and accepts VIH = 2.8 V at VDD = 5 V. Rev 0 measured 300 kOhm from D8 VDD to U6 pin 29 and 0.4 Ohm from D8 VDD to VBUS; U6 bypass continuity was retained and USB operation was normal. | D8 no longer blocks Rev 0 bring-up. The omitted D8-local 100 nF capacitor and unrecorded D8-VDD-to-ground resistance are accepted Rev 0 risks and remain mandatory Rev 1 corrections. | Phil + Copilot | 2026-08-31 |

## Open Questions

| ID | Date | Question | Why It Matters | Owner | Target Date |
|---|---|---|---|---|---|
| Q-001 | 2026-07-06 | What is the confirmed continuous and peak charge/discharge current supported by the selected 12.8V LiFePO4 pack and BMS? | Sets hard current limits for charger and inverter operating envelopes. | Phil + Copilot | 2026-07-13 |
| Q-002 | 2026-07-06 | What minimum instrumentation is available for bring-up (bench supply, DMM count, current probe, scope channels)? | Determines achievable verification depth in early test plans. | Phil + Copilot | 2026-07-13 |
| Q-003 | 2026-07-08 | Should Rev 1 replace the Rev 0 series Schottky PV reverse-polarity stage with an ideal-diode MOSFET block? | Defines the next-revision efficiency path and required schematic/footprint migration work. | Phil + Copilot | 2026-07-20 |
| Q-004 | 2026-07-14 | Closed 2026-07-14: use the wide-input U4 path as the actual Rev 0 `CTRL_3V3` owner, with battery-bus cutoff/UVLO criteria as the selection basis. Keep exact converter PN revision-flexible if footprint/risk constraints require substitution. | Removes owner ambiguity and aligns DEC-013 implementation to one control-rail source path with explicit startup/cutoff behavior targets. | Phil + Copilot | 2026-07-14 |
| Q-005 | 2026-08-25 | Closed 2026-08-26 as DEC-018: the U1 short was caused by routing the board against the `STM32G431CBU6` symbol while fitting `STM32F411CEU6` parts, producing hard supply-pin conflicts through the die. The earlier footprint-defect conclusion (DEC-017) was superseded. | Redirected effort from rework and chip swaps to part/symbol correction, and produced the DEC-020 sourcing strategy plus the mandatory part-substitution gate. | Phil + Copilot | 2026-08-26 |

## Change Log

- 2026-08-26: Added DEC-019 and DEC-020, and added the mandatory Part Substitution Gate (Section 7.2) to `hardware/mppt/kicad-implementation-checklist.md`. Audited the remaining Rev 0 MCU net assignments while verifying `STM32G473CEU6` before ordering. UART is correct (U3 pin names are from the bridge perspective, so `PA9`/TX to bridge RXD and `PA10`/RX to bridge TXD is proper). I2C is swapped at the MCU and is logged as DEC-019. `PB11` (pad 24) is tied to `PWR_NEG` and must never be configured as an output. `PB8`/BOOT0 (pad 46) floats, which is acceptable at default G4 option bytes (`nBOOT_SEL=1`).
- 2026-08-26: Added DEC-018 and superseded DEC-017. Confirmed true root cause of the U1 short: the Rev 0 board was routed against the `STM32G431CBU6` symbol while `STM32F411CEU6` parts were fitted. The DEC-014 migration changed only the `Value`/`MP` text fields, not the symbol `lib_id`, so the pin map was never updated. Verified against KiCad's official `STM32F411CEUx` library: pads 23 and 35 carry `CTRL_3V3` but are `VSS` on F411, and pad 24 carries `PWR_NEG` but is `VDD` on F411, creating two hard short paths through the die. Additional consequences of the same mismatch: `VSSA` (pad 8) and `VDDA` (pad 9) unconnected, `VCAP1` (pad 22) has no capacitor, `BOOT0` (pad 44) driven by `I2C DATA`, `BOOT1` (pad 20) tied high, and `VDD` (pad 36) wired to `SWDIO`. Existing Rev 0 boards are correctly routed for `STM32G431CBU6`; no rework can make `STM32F411CEU6` work on this layout.
- 2026-08-26: Added DEC-017 and closed Q-005. Cross-testing confirmed the U1 `CTRL_3V3`-to-`PWR_NEG` short is a Rev 0 footprint/design-level defect, not a single bad chip or single bad board: the original chip on the original board, a new spare chip on the original board, and the original chip on a second unpopulated board all read the same short. Stopped further chip-swap troubleshooting. Next step for existing Rev 0 boards is targeted salvage rework (cut the suspect copper bridge at the pad 1/48 or pad 24/25 corner and verify with U1 off, or pre-dam the exposed-pad clearance with Kapton/solder-mask pen before reflow); DEC-016 remains the permanent Rev 1 footprint fix.
- 2026-08-26: Added DEC-016. Rev 0 bench debugging on U1 suggests the pad 24/49 corner (`PWR_NEG` break-out next to the exposed pad, same net) may act as a solder-migration channel under the package toward the pad 1/48 (`CTRL_3V3`) corner during reflow. Rev 1 will add exposed-pad relief vias and wider solder-mask dams at all four corners for fine-pitch QFN footprints, starting with the STM32 placement.
- 2026-08-26: Updated Q-005 with a planned isolation test: mount the current suspect U1 (not the guarded spare) on a second, otherwise unpopulated Rev 0 board of the same layout/fab lot, after confirming that board reads open at `CTRL_3V3`-to-`PWR_NEG` with nothing installed. A short reappearing there would confirm the chip is bad across two boards; a clean reading would point to a footprint-level defect specific to the original board.
- 2026-08-26: Corrected Q-005. The prior "no shorted pins" check was performed on the isolated chip, not bare board pads. Since both the isolated chip and the bare board test clean individually, but a clean reseated joint still reads 0.7 ohm, the leading theories shift to a footprint-level cause (solder-mask clearance, thermal-via wicking, or U1 bridging two otherwise-separate copper segments) rather than a simple bad IC. Decision branch: try a replacement U1; if the new chip also reads 0.7 ohm once mounted, treat the fault as board-located at that footprint and stop further chip swaps.
- 2026-08-26: Updated Q-005 with confirmed diagnostic result. Bare-board pin-to-pad-49 continuity checks with U1 removed show no shorted pins, and a full rework cycle (wick, alcohol clean, fresh low-temp paste, clean reseat) still reads 0.7 ohm every time U1 is reinstalled. PCB and solder-joint causes are ruled out; the short is internal to this specific U1 unit. Action: replace U1 rather than continue rework; use ESD precautions and minimize reflow cycles on the replacement part.
- 2026-08-25: Added Q-005: Rev 0 bench bring-up found `CTRL_3V3` at approximately 0.7 ohm to `PWR_NEG`, isolated to U1. Bare board reads approximately 2.5 kohm with U1 removed, so the fault is at the U1 solder interface or the IC itself, not the PCB. Pad-to-net mapping confirms pads 1 and 48 (`CTRL_3V3`) are the two perimeter pads adjacent to the exposed thermal pad (pad 49, `PWR_NEG`). Rework is by hot air station; an iron is used only to pre-tin lead pads before hot air reflow. Root cause not yet confirmed; board bring-up remains blocked at Stage A/B until resolved.
- 2026-08-08: Added DEC-015 and the Wi-Fi coprocessor architecture. The ESP32-C3 development module is powered from `CTRL_5V`; the STM32 remains the charger and safety owner.
- 2026-07-20: Added legacy cleanup backlog defaults and session sequencing for the LM51772-era schematic cleanup pass; current working outcome is to keep `CTRL_PWM_MAIN`, `CTRL_EN_CHG`, `FAULT_OCP`, and `FAULT_OVP`, delete `V_in_ON` unless the Q2 legacy branch is intentionally retained, and treat U2 control-owner role as delete/deprecate.
- 2026-07-20: Refined control/fault ownership cleanup defaults: `CTRL_EN_CHG` remains a hardware-backed MCU enable line, `FAULT_OCP` and `FAULT_OVP` remain hardware protection signals with optional firmware mirroring, and `V_in_ON` defaults to delete unless the legacy `U2/Q2` branch is intentionally preserved.
- 2026-07-20: Added U6 helper-net cleanup defaults: treat U6 as active in the current Rev 0 notes, close `U6_VCC2` with a real decoupler and `U6_FLT` with a pull-up, and keep `U6_SYNC`, `U6_DTRK`, and `U6_RST` only if they remain intentional straps.
- 2026-07-20: Verified the U6 helper-net pass against the live schematic. The FLT helper path and VCC2 helper rail already exist in the schematic, so no additional wiring edit was needed in this batch; keep the current arrangement and document any future strap changes separately.
- 2026-07-14: Closed Q-004 by selecting the U4 wide-input path as Rev 0 `CTRL_3V3` owner using battery-bus-native cutoff/UVLO criteria; exact converter PN remains revision-flexible within the same architecture class.
- 2026-07-14: Added Q-004 to explicitly close the remaining converter-owner ambiguity inside DEC-013; current schematic has U2 as provisional `CTRL_3V3` owner while U4 now references `CTRL_SUPPLY_IN` as the intended wide-input path.
- 2026-07-14: Closed DEC-013 for Rev 0 MCU supply path: wide-input buck primary control rail with PV-first runtime behavior and protected USB fallback for bench bring-up.
- 2026-07-10: Closed DEC-005 to STM32G431 for Rev 0 baseline control MCU with revision-flexible re-evaluation policy.
- 2026-07-08: Added Sheet 4 sensing/control wiring map to start Zone D net-boundary implementation with placeholder control ownership while DEC-005 remains deferred.
- 2026-07-08: Locked converter revision scope: Rev 0 asynchronous buck baseline; synchronous converter and gate-driver architecture deferred to Rev 1.
- 2026-07-08: Reframed DEC-012/Q-003 as Rev 1 optimization items and removed them as Rev 0 pre-routing blockers.
- 2026-07-07: Added Sheet 2 buck power-stage component picks (Q1, D3, L1, C4-C7, R1/C8) with starter electrical targets for immediate symbol placement.
- 2026-07-07: Added Sheet 2 buck power-stage wiring map and extended net plan with implementation nets for protected input and gate-drive path.
- 2026-07-07: Added PV input wiring map with explicit net-by-net symbol connectivity for Sheet 1 implementation.
- 2026-07-07: Added DEC-012/Q-003 to track ideal-diode upgrade work.
- 2026-07-07: Chosen first-pass PV input stage parts: 2-pin terminal block, 10 A fuse, series Schottky reverse protection, 64 V TVS, and 63 V input capacitors.
- 2026-07-07: Added buck symbol placement checklist to drive the first KiCad schematic draw order.
- 2026-07-06: Added GitHub reference review notes for MPPT layout and schematic study, with usage constraints to avoid blind copying.
- 2026-07-06: Added buck topology decision notes and explicit low-irradiance/headroom checks before fully closing DEC-003.
- 2026-07-06: Closed DEC-004 with series panel wiring baseline and narrowed DEC-003 to a buck-preferred path pending controller voltage-class confirmation.
- 2026-07-06: Captured Renogy 100W N-Type panel electrical data in the MPPT envelope worksheet and interface assumptions for DEC-003/DEC-004 analysis.
- 2026-07-06: Added MPPT envelope decision worksheet and decision update template to accelerate DEC-003/DEC-004 closure.
- 2026-07-06: Added KiCad implementation checklist to enforce draw-annotate-verify save-point workflow for MPPT exploration.
- 2026-07-06: Added MPPT schematic execution scaffold (schematic-notes, net-plan, component-shortlist-template) for rapid KiCad start.
- 2026-07-06: Added MPPT first-pass block diagram with requirement/decision mapping to start Phase 1 schematic exploration.
- 2026-07-06: Added MPPT hardware kickoff artifacts and DEC-011 temporary bounds policy for active exploration.
- 2026-07-06: Added Phase 1 kickoff plan and DEC-010 rapid execution policy with conservative fallback rules.
- 2026-07-06: Added Phase 0 exit decision (DEC-009), validation-plan, and phase-0-exit-review artifacts.
- 2026-07-06: Added compact requirements traceability matrix and initial test/bringup-checklist tied to REQ-SAF-006 and REQ-VAL-001.
- 2026-07-06: Added `requirements.md` and `architecture.md`; decision references now mapped for Phase 0.
- 2026-07-06: Initial log created from handoff baseline and concept open decisions.
