Phil-CIA/Solar-Project-200w/docs/phase-0-exit-review.md

# Solar Project 200W - Phase 0 Exit Review

Date: 2026-07-06
Owners: Phil + Copilot
Phase: Planning and concept baseline

## 1. Exit Gate Summary

Overall status: PASS with deferred implementation decisions tracked.

## 2. Gate Checklist

| Gate Item | Status | Evidence |
|---|---|---|
| Requirements drafted with measurable targets and verification methods | Pass | docs/requirements.md |
| Architecture drafted with subsystem boundaries and interface mapping | Pass | docs/architecture.md |
| Decisions log active with dated entries and deferred item ownership | Pass | docs/decisions-log.md |
| Traceability matrix connecting requirements to architecture/decisions | Pass | requirements section 9 |
| Bring-up checklist available for staged validation | Pass | docs/test/bringup-checklist.md |
| Initial validation test plan available | Pass | docs/test/validation-plan.md |
| Safety controls represented in requirements and architecture | Pass | REQ-SAF set + architecture section 4 |

## 3. Deferred Items Carried Into Next Phase

- DEC-003: MPPT topology final selection (buck vs buck-boost)
- DEC-004: Panel wiring final selection (series vs parallel)
- DEC-005: Charger control partition final selection
- Q-001: Confirm battery/BMS continuous and peak current envelope
- Q-002: Confirm instrumentation capability for test depth

## 4. Next Phase Start Definition

Next phase focus: implementation exploration for MPPT path with controlled risk.

First actions:
1. Resolve Q-001 and Q-002 to establish hard limits.
2. Finalize DEC-004 panel wiring strategy and then DEC-003 topology.
3. Build MPPT schematic exploration package and component shortlist.
4. Run VAL-001 through VAL-004 before hardware build commitment.

## 5. Exit Decision

Phase 0 is complete. Proceed to next phase with deferred decisions tracked in decisions log and reviewed weekly.
