Phil-CIA/Solar-Project-200w/docs/SOLAR_HANDOFF_2026-07-08.md

# Solar Project 200W - Handoff

## Session Closeout - 2026-07-08

This stop closed the current planning-to-implementation transition and locked revision scope so schematic execution can continue without architecture churn.

## What Was Completed

1. Rev boundary locked for converter implementation:
- Rev 0: asynchronous buck baseline
- Rev 1: synchronous converter and dedicated gate-driver upgrade path

2. Scope and decision consistency updated across core docs:
- `docs/decisions-log.md`
- `docs/phase-1-kickoff.md`
- `hardware/mppt/sheet2-component-picks.md`
- `hardware/mppt/buck-power-stage-wiring-map.md`
- `hardware/mppt/kicad-implementation-checklist.md`

3. Routing blocker removed for current revision:
- DEC-012/Q-003 are now Rev 1 optimization items, not Rev 0 pre-routing blockers.

## Verified State At Stop

- Sheet 2 docs are aligned to asynchronous Rev 0 implementation.
- Checklist gates now allow Rev 0 routing progression.
- Decisions log reflects explicit Rev 0 vs Rev 1 scope.
- Edited markdown files validated with no errors.

## Current Objective At Stop

Begin Sheet 2 symbol placement in KiCad using the locked Rev 0 asynchronous buck baseline.

## Next Session Priority Order

1. Place Sheet 2 core power symbols in KiCad:
- Q1, D3, L1, C4, C5, C6, C7, R1, C8

2. Wire nets exactly per mapping docs:
- `hardware/mppt/buck-power-stage-wiring-map.md`
- `hardware/mppt/net-plan.md`

3. Confirm note annotations on sheet:
- ASSUME async freewheel path
- DECISION Rev 0 async lock
- VERIFY voltage/current margins

4. Run implementation checklist save-point protocol:
- update `hardware/mppt/schematic-notes.md`
- update decisions log only if new trade-offs are introduced

## First Action Next Session

Open `HANDOFF.md`, then open `hardware/kicad/solar-project/Solar Project.kicad_sch` and place Q1, D3, and L1 first around `MPPT_SW_NODE`.
