Phil-CIA/Solar-Project-200w/docs/SOLAR_HANDOFF_2026-07-06.md

# Solar Project 200W - Handoff

## Session Closeout - 2026-07-06

This stop finalized repository bootstrap and aligned handoff artifacts to the active Solar project workspace.

## What Was Completed

1. Solar repo scaffold established and pushed.
2. Active KiCad project imported to `hardware/kicad/solar-project/`.
3. Transient KiCad local-state files excluded from source control.
4. Root handoff files created for future restart continuity.
5. Existing concept/prompt docs updated to current-state continuation.

## Verified State At Stop

- Committed KiCad source files present:
  - `Solar Project.kicad_pro`
  - `Solar Project.kicad_sch`
  - `Solar Project.kicad_pcb`
- Current continuation focus is documentation/planning, not implementation.

## Current Objective At Stop

Define project requirements and architecture with enough precision to support safe, staged technical execution.

## Next Session Priority Order

1. Requirements document with measurable targets.
2. Architecture document with clear subsystem boundaries.
3. Decisions log with open questions and rationale.
4. README links and navigation updates.

## First Action Next Session

Create `docs/requirements.md` using the 200W baseline and safety priorities as primary inputs.
