Phil-CIA/Solar-Project-200w/docs/WBDesignLM851772.pdf

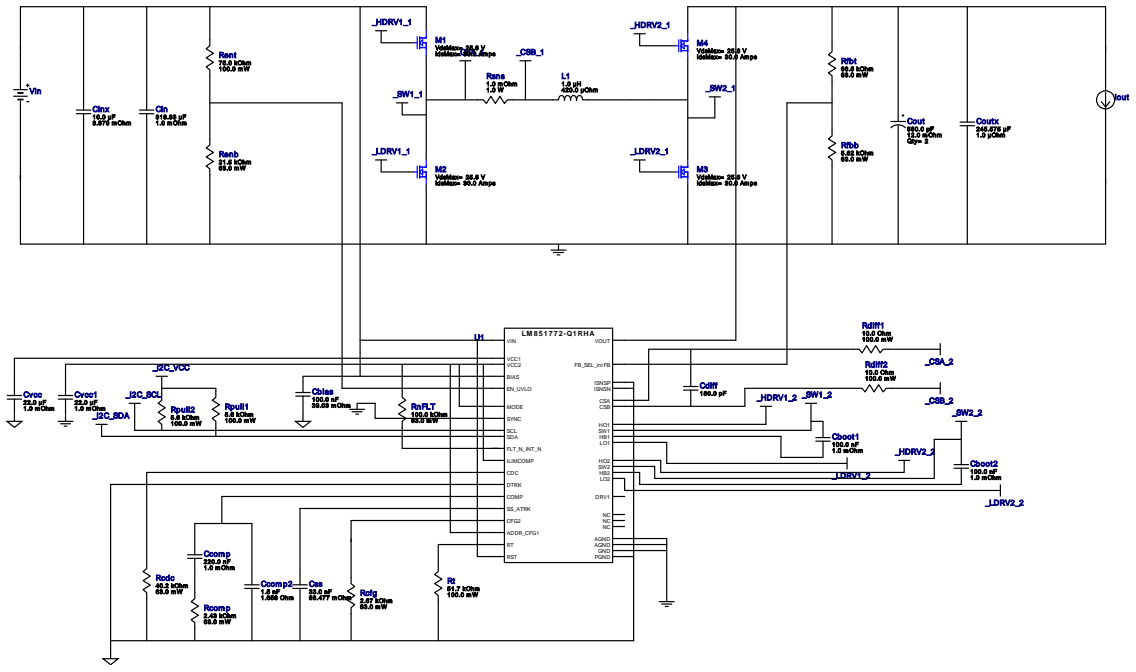
[picture p6: figure]
Css 33.0 nF 98.477 m Ohm; Ccom p 220.0 nF 1.0 m Ohm; LM 8 5 1 7 7 2 -Q1 RHA; VCC1; SS_ATRK; SYNC; DTRK; SDA; SCL; MODE; CFG2; ADDR_CFG1; CDC; FLT_N_INT_N; COMP; FB_SEL_intFB; AGND; ILIMCOMP; VOUT; ISNSN; ISNSP; CSB CSA; PGND; VCC2; DRV1; BIAS; EN_UVLO; RST; VIN; GND; Cinx 10.0 µF 3.979 m Ohm; _LDRV1_2; Coutx 245.575 µF 1.0 µOhm; _HDRV2_2; Cvcc 22.0 µF 1.0 m Ohm; _HDRV1_1; Cboot1 100.0 nF 1.0 m Ohm; Cbias 100.0 nF 39.03 m Ohm; _LDRV2_2; _CSA_2; _LDRV2_1; Cin 318.63 µF 1.0 m Ohm; _HDRV2_1; _CSB_1; L1 1.0 µH 420.0 µOhm; Cvcc1 22.0 µF 1.0 m Ohm; M2 VdsMax= 25.6 V IdsMax= 30.0 Am ps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

Copyright © 2026, Texas Instruments Incorporated | 1 | ti.com/webench

WEBENCH®
Design Report LM851772QRHARQ1 : LM851772QRHARQ1 6V-42V to 12.80V @ 20A July 15, 2026 11:59:51 GMT-05:00

## WEBENCH ® Design Report

Design : 5 LM851772QRHARQ1
LM851772QRHARQ1 6V-42V to 12.80V @ 20A

VinMin = 6.0V
VinMax = 42.0V
Vout = 12.8V
Iout = 20.0A

Device = LM851772QRHARQ1
Topology = Buck_Boost
Created = 2026-07-15 11:43:04.325 BOM Cost = NA
BOM Count = 37
Total Pd =
1. The LM851772-Q1features AutoMode for better light load efficiency. The operating point calculated in AutoMode configuration are estimates

### Design Alerts

Component Selection Information
The LM851772-Q1 is qualified for Automotive applications. All passives and other components selected in this design may not be qualified for Automotive applications. The user is required to verify that all components in the design meet the qualification and safety requirements for their specific application.

## Electrical BOM

Name | Manufacturer | Part Number | Properties | Qty Price | Footprint
Cbias | TDK | C1005X7R1H104K050BB (https://product.tdk.com/ja/search/capacitor/ceramic/mlcc/info?part%5Fno%3DC1005X7R1H104K050BB) Series= X7R | Cap= 100.0 nF ESR= 39.03 mOhm VDC= 50.0 V IRMS= 0.0 A
1 | $0.02
| | | | | 0402 3 mm²
Cboot1 | Taiyo Yuden | EMK107B7104KA-T (http://www.yuden.co.jp/ut/product/pdf/djmk%5Fe.pdf) Series= X7R

Cap= 100.0 nF
ESR= 1.0 mOhm
VDC= 16.0 V
IRMS= 0.0 A

1 $0.01
0603 5 mm²
Cboot2 | Taiyo Yuden | EMK107B7104KA-T (http://www.yuden.co.jp/ut/product/pdf/djmk%5Fe.pdf) Series= X7R

Cap= 100.0 nF
ESR= 1.0 mOhm
VDC= 16.0 V
IRMS= 0.0 A

1 $0.01
0603 5 mm²
Ccomp | MuRata | GRM155R71C224KA12D (http://search.murata.co.jp/Ceramy/PnsearchViewAction.do) Series= X7R

Cap= 220.0 nF
ESR= 1.0 mOhm
VDC= 16.0 V
IRMS= 0.0 A

1 $0.02
0402 3 mm²
Ccomp2 | TDK | CGA2B2X7R1H152K050BA (https://product.tdk.com/en/search/capacitor/ceramic/mlcc/info?part%5Fno%3DCGA2B2X7R1H152K050BA) Series= X7R

Cap= 1.5 nF
ESR= 1.6581 Ohm
VDC= 50.0 V
IRMS= 254.831 mA

1 $0.01
0402 3 mm²

Design

Copyright © 2026, Texas Instruments Incorporated | 2 | ti.com/webench
Name | Manufacturer | Part Number | Properties | Qty Price | Footprint
Cdiff | Kemet | C0805C181K5GACTU (http://www.kemet.com/docfinder?Partnumber%3DC0805C181K5GACTU) Series= C0G/NP0 | Cap= 180.0 pF VDC= 50.0 V IRMS= 0.0 A
1 | $0.01
| | | | | 0805 7 mm²
Cin | CUSTOM | CUSTOM Series= ? | Cap= 318.63 uF ESR= 1.0 mOhm VDC= 50.4 V IRMS= 4.8843 A
1 | NA
| | | | | CUSTOM 0 mm²
Cinx | Taiyo Yuden | MSASU32MSB5106KPNA01 (https://ds.yuden.co.jp/TYCOMPAS/ut/detail?pn%3DMSASU32MSB5106KPNA01%26u%3DM) Series= X5R

Cap= 10.0 uF
ESR= 3.979 mOhm
VDC= 50.0 V
IRMS= 3.4821 A

1 $0.16
1210 15 mm²
Cout | Panasonic | 20SVPF560M Series= SVPF

Cap= 560.0 uF
ESR= 12.0 mOhm
VDC= 20.0 V
IRMS= 5.4 A

2 $1.33

CAPSMT_62_F12 151 mm²
Coutx | CUSTOM | CUSTOM Series= ?

Cap= 245.575 uF
ESR= 1.0 uOhm
VDC= 25.6 V
IRMS= 1.06155 A

1 NA
CUSTOM 0 mm²
Css | TDK | CGA2B3X7R1H333K050BB (https://product.tdk.com/en/search/capacitor/ceramic/mlcc/info?part%5Fno%3DCGA2B3X7R1H333K050BB) Series= X7R

Cap= 33.0 nF
ESR= 98.477 mOhm
VDC= 50.0 V
IRMS= 530.78 mA

1 $0.01
0402 3 mm²
Cvcc | MuRata | GRM188R60J226MEA0D (http://search.murata.co.jp/Ceramy/image/img/A01X/G101/ENG/GRM188R60J226MEA0%2D01.pdf) Series= X5R

Cap= 22.0 uF
ESR= 1.0 mOhm
VDC= 6.3 V
IRMS= 6.0 A

1 $0.04
0603 5 mm²
Cvcc1 | MuRata | GRM188R60J226MEA0D (http://search.murata.co.jp/Ceramy/image/img/A01X/G101/ENG/GRM188R60J226MEA0%2D01.pdf) Series= X5R

Cap= 22.0 uF
ESR= 1.0 mOhm
VDC= 6.3 V
IRMS= 6.0 A

1 $0.04
0603 5 mm²
L1 | Coiltronics | HC3-1R0-R (http://www.cooperbussmann.com/pdf/0250e647%2De4f1%2D4bd5%2Db46c%2Dd9b46529d29e.pdf) | L= 1.0 µH 420.0 µOhm
1 | $6.88

HC3 874 mm²
M1 | NA | IdealFET | VdsMax= 25.6 V IdsMax= 30.0 Amps
1 | NA
KCS0003B 80 mm²
M2 | NA | IdealFET | VdsMax= 25.6 V IdsMax= 30.0 Amps
1 | NA
KCS0003B 80 mm²
M3 | NA | IdealFET | VdsMax= 25.6 V IdsMax= 30.0 Amps
1 | NA
KCS0003B 80 mm²
M4 | NA | IdealFET | VdsMax= 25.6 V IdsMax= 30.0 Amps
1 | NA
KCS0003B 80 mm²
Rcdc | Vishay-Dale | CRCW040240K2FKED (http://www.vishay.com/docs/20035/dcrcwe3.pdf) Series= CRCW..e3 | Res= 40.2 kOhm Power= 63.0 mW Tolerance= 1.0%
1 | $0.01
0402 3 mm²
Rcfg | Vishay-Dale | CRCW04022K67FKED (http://www.vishay.com/docs/20035/dcrcwe3.pdf) Series= CRCW..e3 | Res= 2.67 kOhm Power= 63.0 mW Tolerance= 1.0%
1 | $0.01
0402 3 mm²
Rcfg | Vishay-Dale | CRCW04022K67FKED (http://www.vishay.com/docs/20035/dcrcwe3.pdf) Series= CRCW..e3 | Res= 2.67 kOhm Power= 63.0 mW Tolerance= 1.0%
1 | $0.01
0402 3 mm²

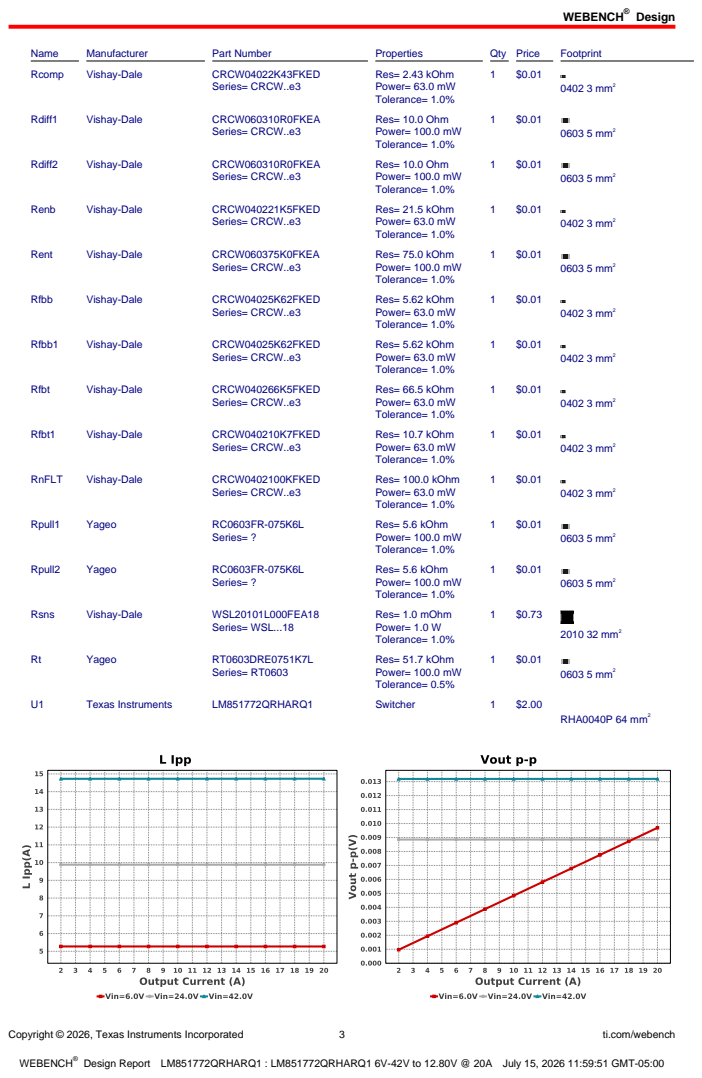
[picture p7: page 3]
Copyright © 2026, Texas Instruments Incorporated; ti.com/webench; Name; Manufacturer; Part Number; Properties; Qty Price; Footprint; Rcomp; Vishay-Dale; CRCW04022K43FKED; Series= CRCW..e3; Res= 2.43 kOhm Power= 63.0 mW Tolerance= 1.0%; 0402 3 mm²; Rdiff1; CRCW060310R0FKEA; Res= 10.0 Ohm Power= 100.0 mW Tolerance= 1.0%; 0603 5 mm²; Rdiff2; Renb; CRCW040221K5FKED; Res= 21.5 kOhm Power= 63.0 mW Tolerance= 1.0%; Rent; CRCW060375K0FKEA; Res= 75.0 kOhm Power= 100.0 mW Tolerance= 1.0%; Rfbb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

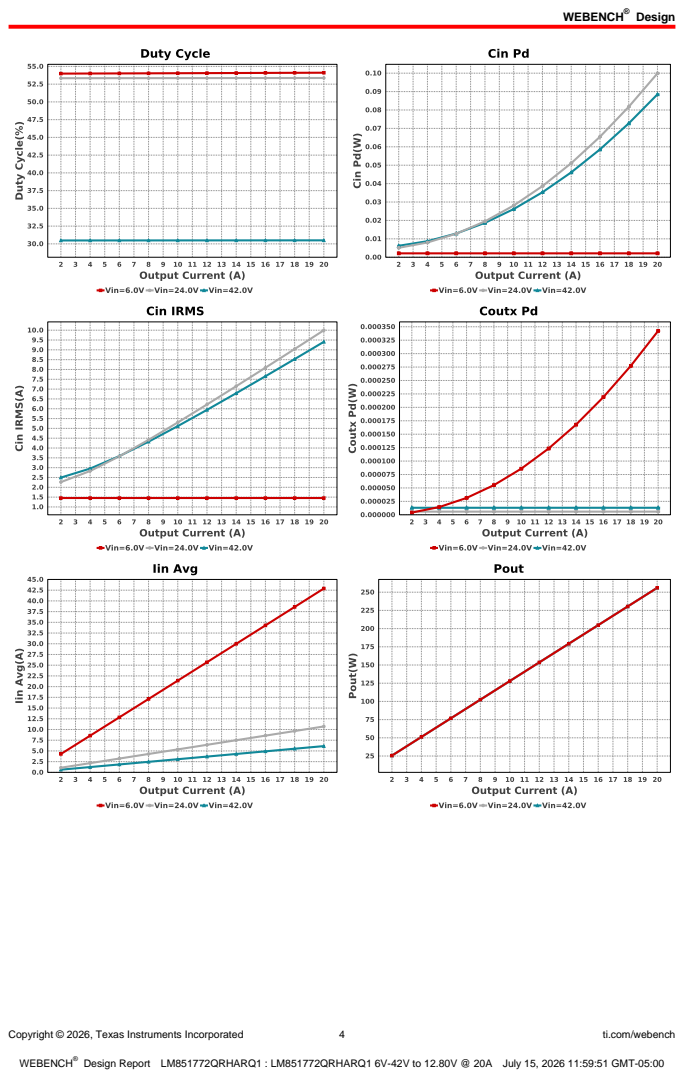
[picture p8: page 4]
Copyright © 2026, Texas Instruments Incorporated; ti.com/webench

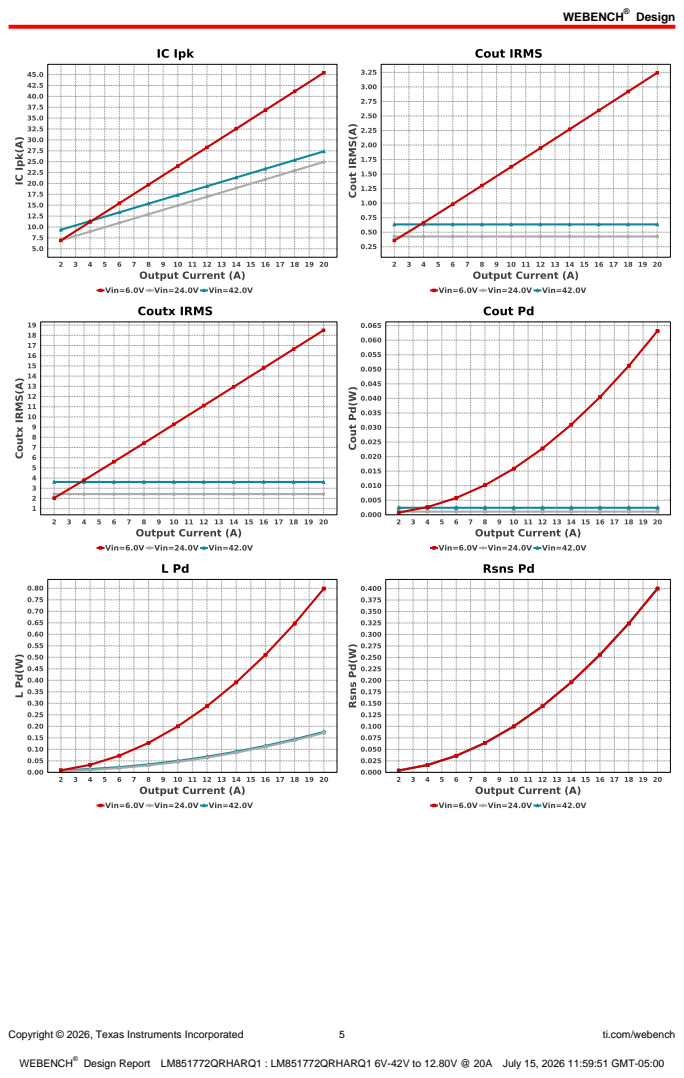
[picture p9: page 5]
Copyright © 2026, Texas Instruments Incorporated; ti.com/webench

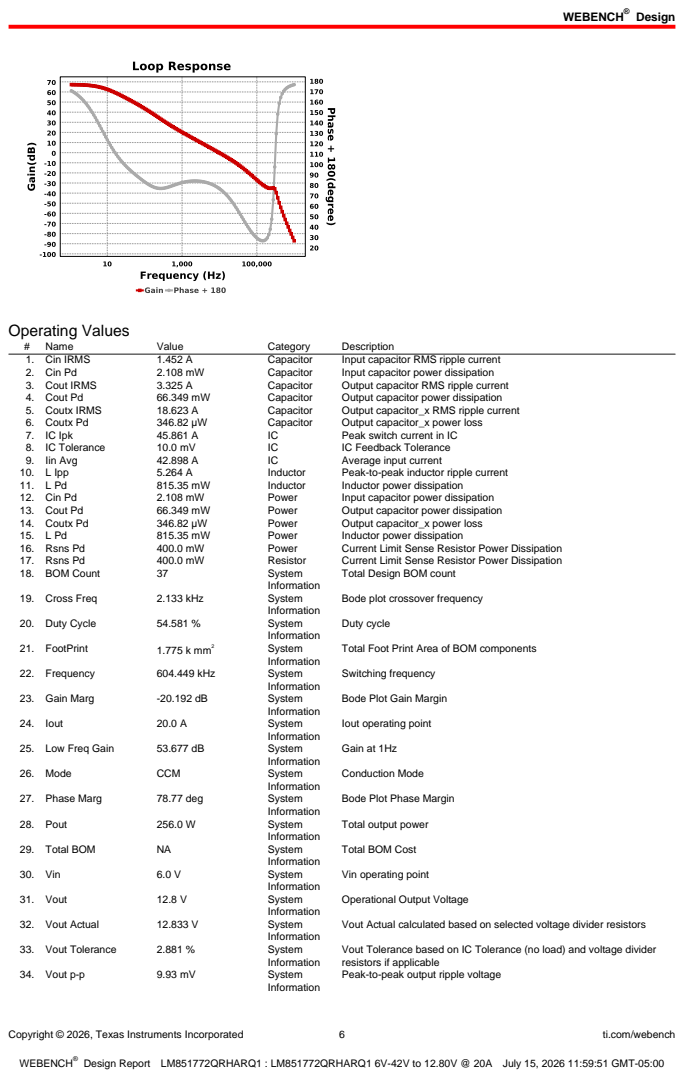
[picture p10: page 6]
Copyright © 2026, Texas Instruments Incorporated; ti.com/webench; Operating Values; Name; Value; Category; Description; 1. Cin IRMS; Capacitor; Input capacitor RMS ripple current; 2. Cin Pd; Input capacitor power dissipation; 3. Cout IRMS; Output capacitor RMS ripple current; 4. Cout Pd; Output capacitor power dissipation; 5. Coutx IRMS; Output capacitor_x RMS ripple current; 6. Coutx Pd; Output capacitor_x power loss; 7. IC Ipk; Peak switch current in IC; 8. IC Tolerance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

Total Design BOM count

Bode plot crossover frequency

Total Foot Print Area of BOM components

Bode Plot Gain Margin

Iout operating point

Bode Plot Phase Margin

Total output power

Total BOM Cost

Vin operating point

Operational Output Voltage

Vout Actual calculated based on selected voltage divider resistors

Vout Tolerance based on IC Tolerance (no load) and voltage divider
resistors if applicable
Peak-to-peak output ripple voltage

Copyright © 2026, Texas Instruments Incorporated | 7 | ti.com/webench

## Design Inputs

Name | Value | Description
Iout | 20.0 | Maximum Output Current
VinMax | 42.0 | Maximum input voltage
VinMin | 6.0 | Minimum input voltage
Vout | 12.8 | Output Voltage
base_pn | LM851772-Q1 | Base Product Number
source | DC | Input Source Type
Ta | 30.0 | Ambient temperature


Copyright © 2026, Texas Instruments Incorporated | 8 | ti.com/webench

## Assembly

## Component Testing

Some published data on components in datasheets such as Capacitor ESR and Inductor DC resistance is based on conservative values that will guarantee that the components always exceed the specification. For design purposes it is usually better to work with typical values. Since this data is not always available it is a good practice to measure the Capacitance and ESR values of Cin and Cout, and the inductance and DC resistance of L1 before assembly of the board. Any large discrepancies in values should be electrically simulated in WEBENCH to check for instabilities and thermally simulated in WebTHERM to make sure critical temperatures are not exceeded.

## Soldering Component to Board

If board assembly is done in house it is best to tack down one terminal of a component on the board then solder the other terminal. For surface mount parts with large tabs, such as the DPAK, the tab on the back of the package should be pre-tinned with solder, then tacked into place by one of the pins. To solder the tab town to the board place the iron down on the board while resting against the tab, heating both surfaces simultaneously. Apply light pressure to the top of the plastic case until the solder flows around the part and the part is flush with the PCB. If the solder is not flowing around the board you may need a higher wattage iron (generally 25W to 30W is enough).

## Initial Startup of Circuit

It is best to initially power up the board by setting the input supply voltage to the lowest operating input voltage 6.0V and set the input supply's current limit to zero. With the input supply off connect up the input supply to Vin and GND. Connect a digital volt meter and a load if needed to set the minimum Iout of the design from Vout and GND. Turn on the input supply and slowly turn up the current limit on the input supply. If the voltage starts to rise on the input supply continue increasing the input supply current limit while watching the output voltage. If the current increases on the input supply, but the voltage remains near zero, then there may be a short or a component misplaced on the board. Power down the board and visually inspect for solder bridges and recheck the diode and capacitor polarities. Once the power supply circuit is operational then more extensive testing may include full load testing, transient load and line tests to compare with simulation results.

## Load Testing

The setup is the same as the initial startup, except that an additional digital voltmeter is connected between Vin and GND, a load is connected between Vout and GND and a current meter is connected in series between Vout and the load. The load must be able to handle at least rated output power + 50% ( 7.5 watts for this design). Ideally the load is supplied in the form of a variable load test unit. It can also be done in the form of suitably large power resistors. When using an oscilloscope to measure waveforms on the prototype board, the ground leads of the oscilloscope probes should be as short as possible and the area of the loop formed by the ground lead should be kept to a minimum. This will help reduce ground lead inductance and eliminate EMI noise that is not actually present in the circuit.

## Design Assistance

1. Master key : 8798C1FA2C1E78B872875FCFEF5BDD77[v1]
2. LM851772-Q1 Product Folder : https://www.ti.com/product/LM851772%2DQ1 : contains the data sheet and other resources.

Copyright © 2026, Texas Instruments Incorporated | 9 | ti.com/webench

Important Notice and Disclaimer

TI provides technical and reliability data (including datasheets), design resources (including reference designs), application or other design advice, web tools, safety information, and other resources AS IS and with all faults, and disclaims all warranties. These resources are intended for skilled developers designing with TI products. You are solely responsible for (1) selecting the appropriate TI products for your application, (2) designing, validating and testing your application, and (3) ensuring your application meets applicable standards, and any other safety, security, or other requirements.

These resources are subject to change without notice. TI grants you permission to use these resources only for development of an application that uses the TI products described in the resource. Other reproduction and display of these resources is prohibited. No license is granted to any other TI intellectual property right or to any third party intellectual property right. TI disclaims responsibility for, and you will fully indemnify TI and its representatives against, any claims, damages, costs, losses, and liabilities arising out of your use of these resources.

Providing these resources does not expand or otherwise alter TI's applicable Terms of Sale or other applicable terms available either on ti.com or provided in conjunction with TI products.
