Phil-CIA/Solar-Project-200w/hardware/kicad/solar-project/spice/pv_switch_gate_drive.asc

D1: diode; DZ
M2: nmos; NMOS2
R40: res; 100k
R41: res; 10
R42: res; 10
R43: res; 100k
RSRC: res; 1Meg
V1: voltage; {VIN}
V3: voltage; 3.3
V4: voltage; {VCTRL}
Named nets: 0, PVHI, Q2D, Q2G, U2GATE, U2SRC, CTRL3V3, VCTRL
.param VIN=12 VCTRL=0
.op
.save V(PVHI) V(Q2D) V(Q2G) V(U2GATE) V(U2SRC) V(U2GATE,U2SRC)
.model NMOS2 NMOS (VTO=1.6 KP=0.6M RD=0.1 RS=0.1)
.model DZ D (IS=1e-15 BV=12 IBV=1e-3 CJO=100p VJ=0.7)
